thestumbler/serial-squid/docs/squid-pinouts.ods

Sheet: PORTS
SEQ PORT | SEQ PIN | P176x | PORT | BIT | FUNC1 | FUNC2 | FUNC3
1 | 1 | 46 | 0 | 0 | RD1 | TXD3 | SDA1
2 | 2 | 47 | 0 | 1 | TD1 | RXD3 | SCL1
3 | 3 | 98 | 0 | 2 | TXD0 | AD0.7 | N/A
4 | 4 | 99 | 0 | 3 | RXD0 | AD0.6 | N/A
5 | 5 | 81 | 0 | 4 | I2SRX_CLK | RD2 | CAP2.0
6 | 6 | 80 | 0 | 5 | I2SRX_WS | TD2 | CAP2.1
7 | 7 | 79 | 0 | 6 | I2SRX_SDA | SSEL1 | MAT2.0
8 | 8 | 78 | 0 | 7 | I2STX_CLK | SCK1 | MAT2.1
9 | 9 | 77 | 0 | 8 | I2STX_WS | MISO1 | MAT2.2
10 | 10 | 76 | 0 | 9 | I2SRTX_SDA | MOSI1 | MAT2.3
11 | 11 | 48 | 0 | 10 | TXD2 | SDA2 | MAT3.0
12 | 12 | 49 | 0 | 11 | RXD2 | SCL2 | MAT3.1
13 | N/A | N/A | 0 | 12 | N/A | N/A | N/A
14 | N/A | N/A | 0 | 13 | N/A | N/A | N/A
15 | N/A | N/A | 0 | 14 | N/A | N/A | N/A
16 | 13 | 62 | 0 | 15 | TXD1 | SCK0 | SCK
17 | 14 | 63 | 0 | 16 | RXD1 | SSEL0 | SSEL
18 | 15 | 61 | 0 | 17 | CTS1 | MISO0 | MISO
19 | 16 | 60 | 0 | 18 | DCD1 | MOSI0 | MOSI
20 | 17 | 59 | 0 | 19 | DSR1 |  | SDA1
21 | 18 | 58 | 0 | 20 | DTR1 |  | SCL1
22 | 19 | 57 | 0 | 21 | RI1 |  | RD1
23 | 20 | 56 | 0 | 22 | RTS1 |  | TD1
24 | 21 | 9 | 0 | 23 | AD0.0 | I2SRX_CLK | CAP3.0
25 | 22 | 8 | 0 | 24 | AD0.1 | I2SRX_WS | CAP3.1
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
