thestumbler/serial-squid/docs/connector-figure-with-table.odp

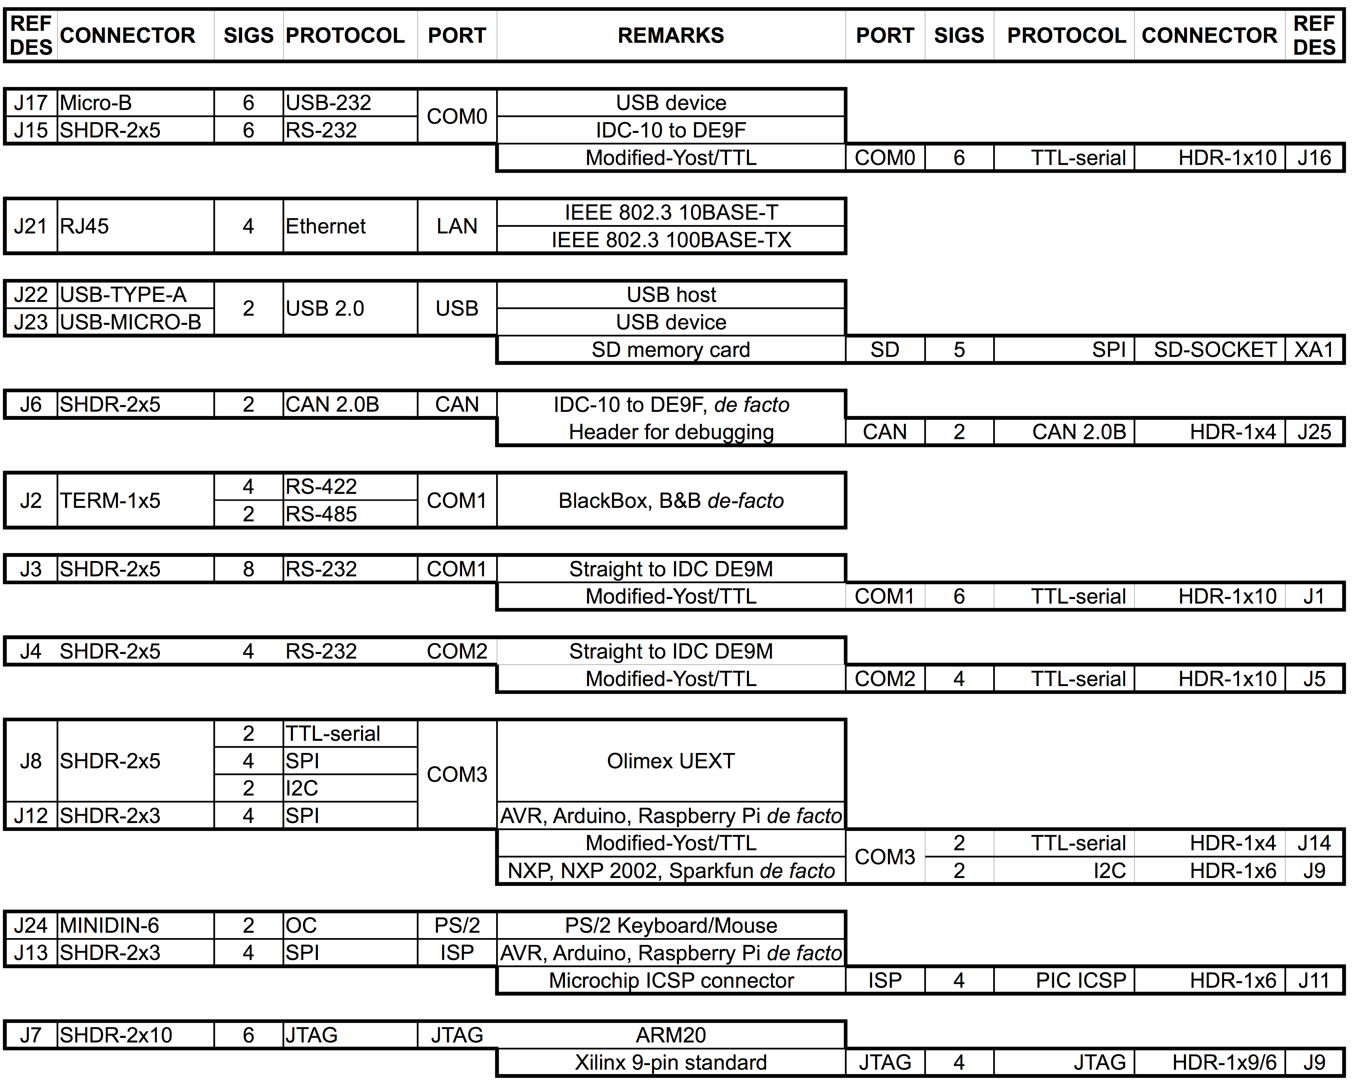
[picture p1: figure]

Serial Squid - Interface Connections

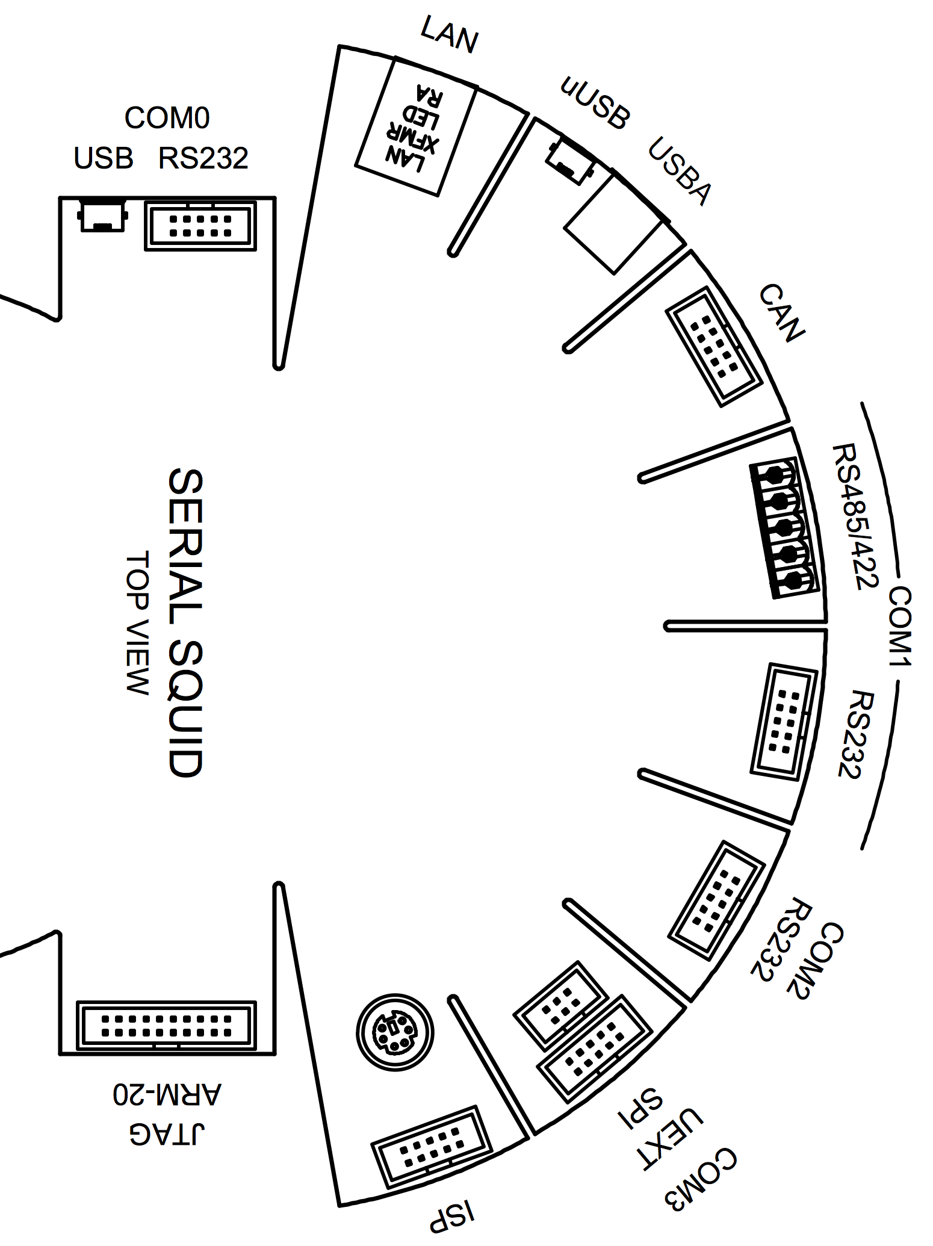
[picture p2: figure]
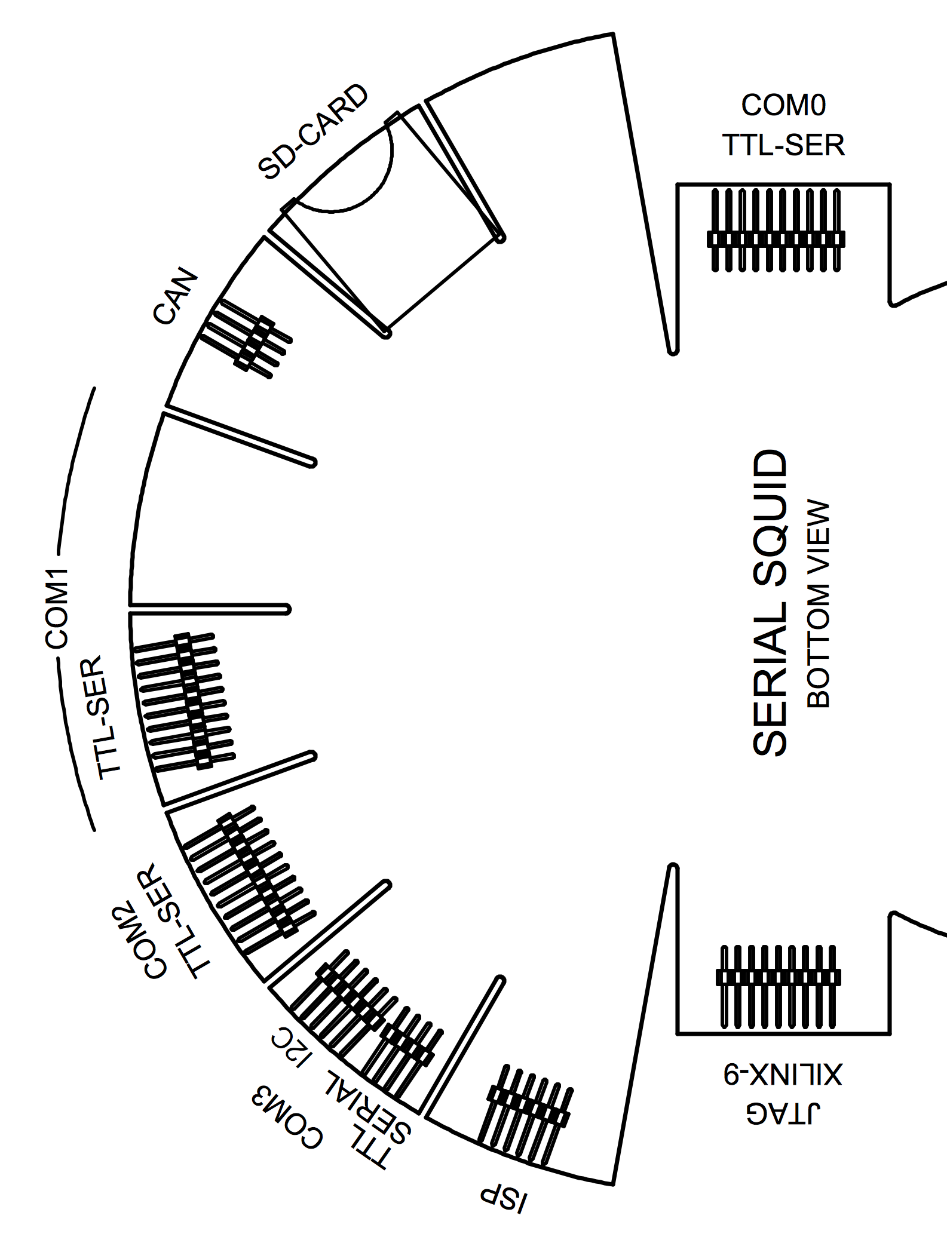
[picture p3: figure]
