thestumbler/serial-squid/parts/con-sd5020-sd-card-socket-smt.pdf

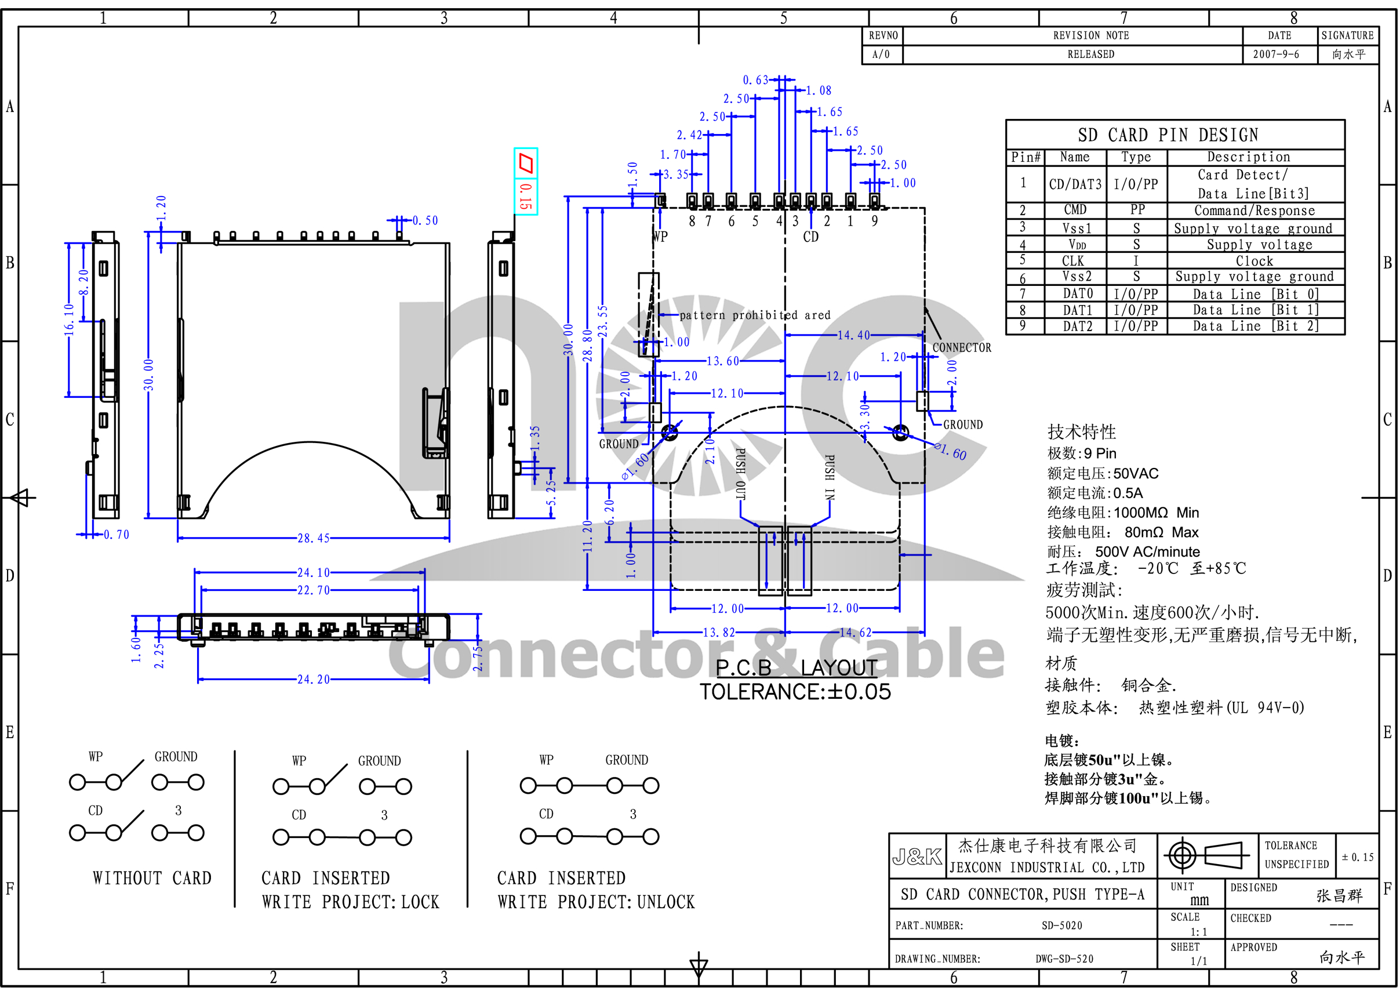
[picture p9: page 1]
