thestumbler/serial-squid/parts/usb-type-a-flat.pdf

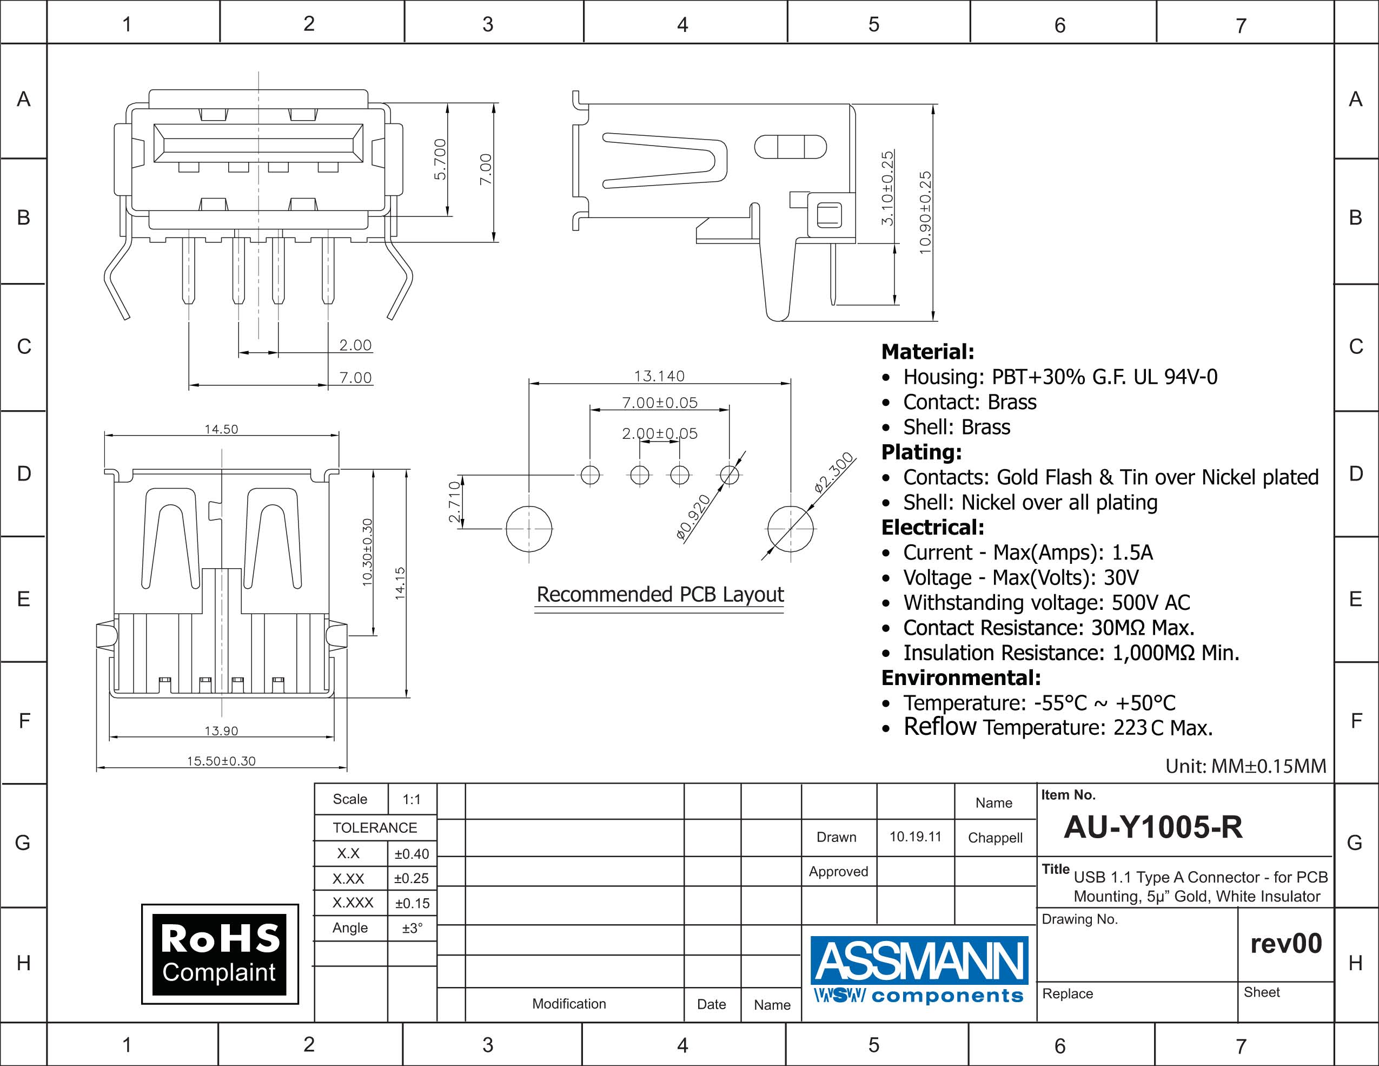
[picture p10: page 1]
