thestumbler/serial-squid/parts/pkg-diodes-inc-SOT23.jpg

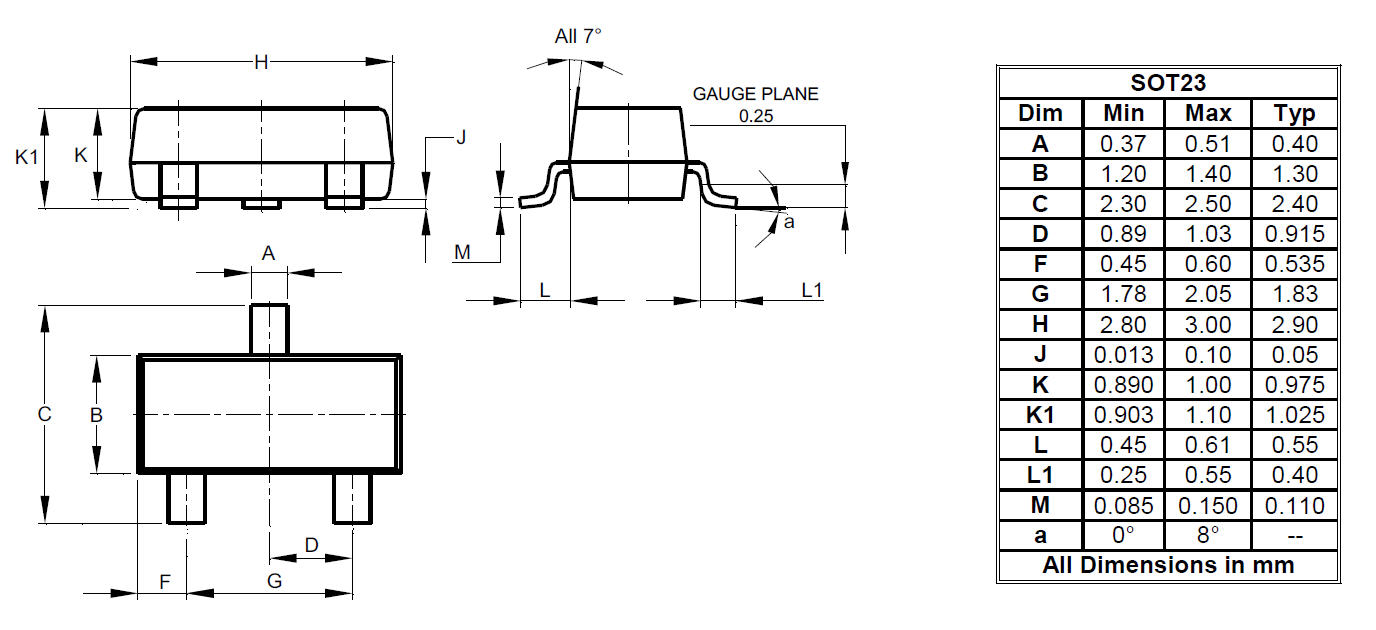
parts/pkg-diodes-inc-SOT23.jpg
