thestumbler/serial-squid/parts/pkg-diodes-inc-SOT323.jpg

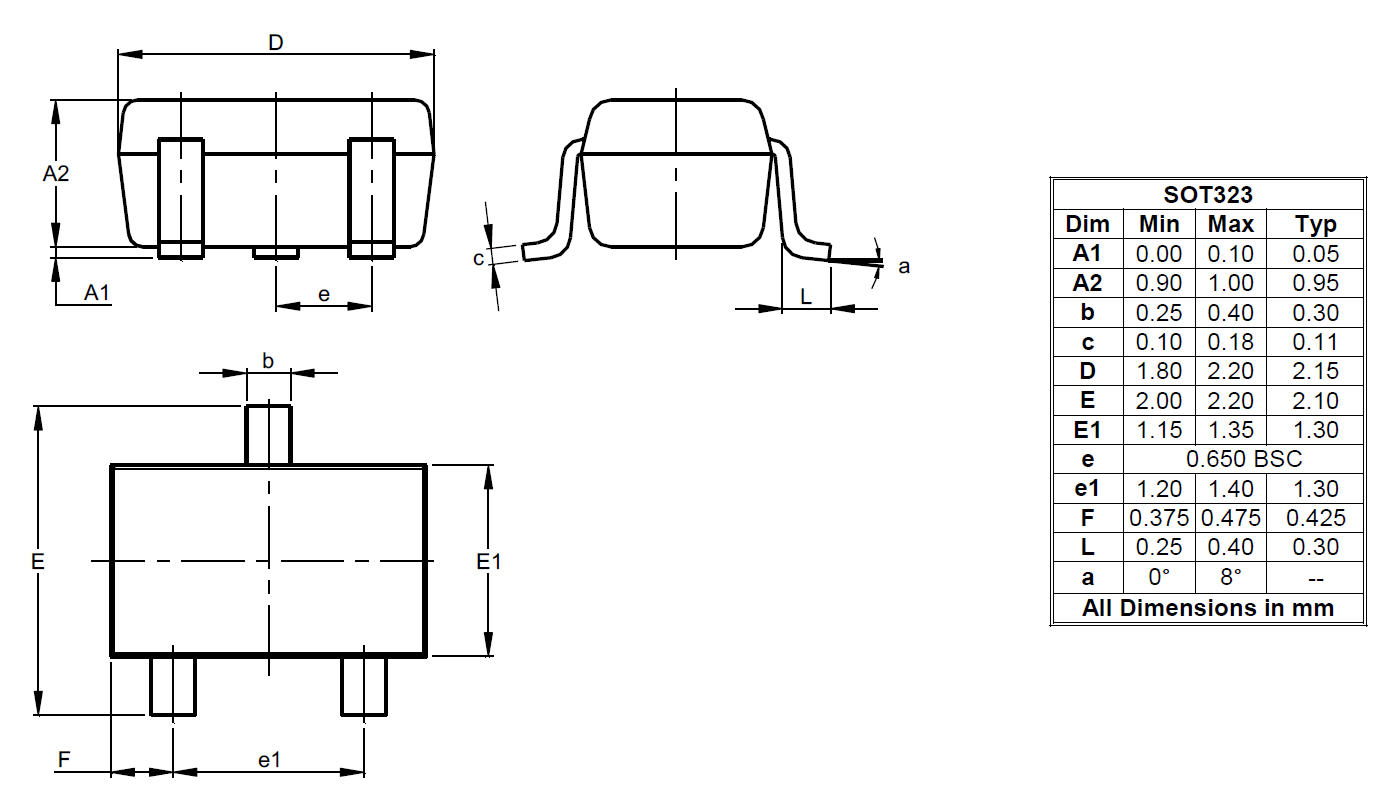
parts/pkg-diodes-inc-SOT323.jpg
