thestumbler/serial-squid/docs/prints/draft2-bot.png

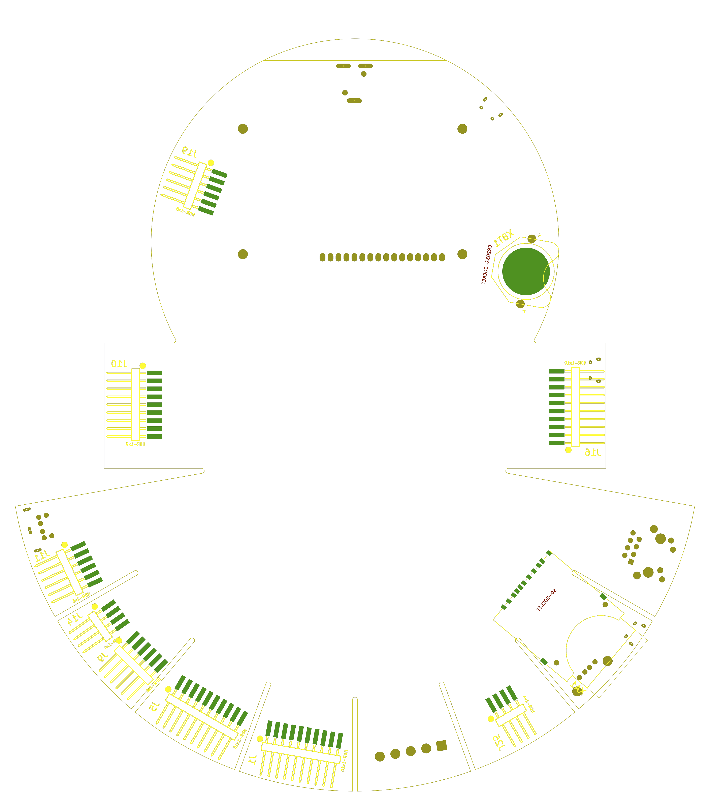
docs/prints/draft2-bot.png
