thestumbler/serial-squid/mech/squid-how-to-draw.png

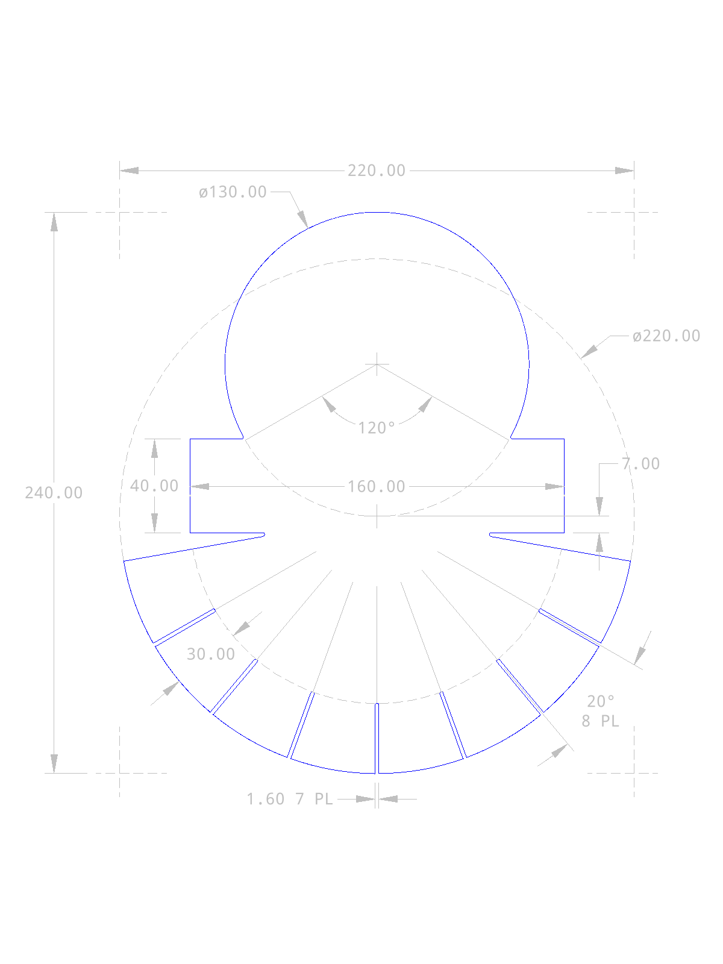
mech/squid-how-to-draw.png
