thestumbler/serial-squid/docs/connector-figure.pdf

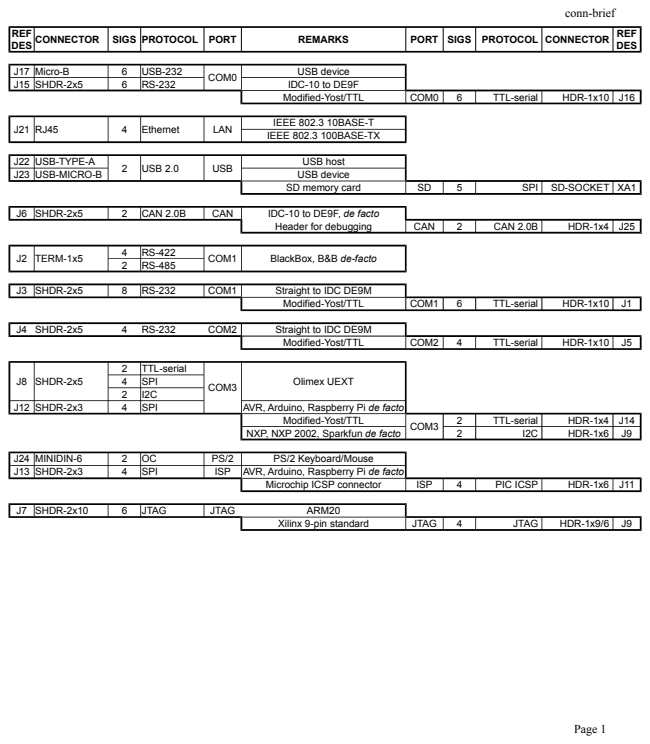
[picture p16: page 1]

IDC-10 to DE9F, de facto

AVR, Arduino, Raspberry Pi de facto

NXP, NXP 2002, Sparkfun de facto
