thestumbler/serial-squid/docs/squid-drawing-bot-view.pdf

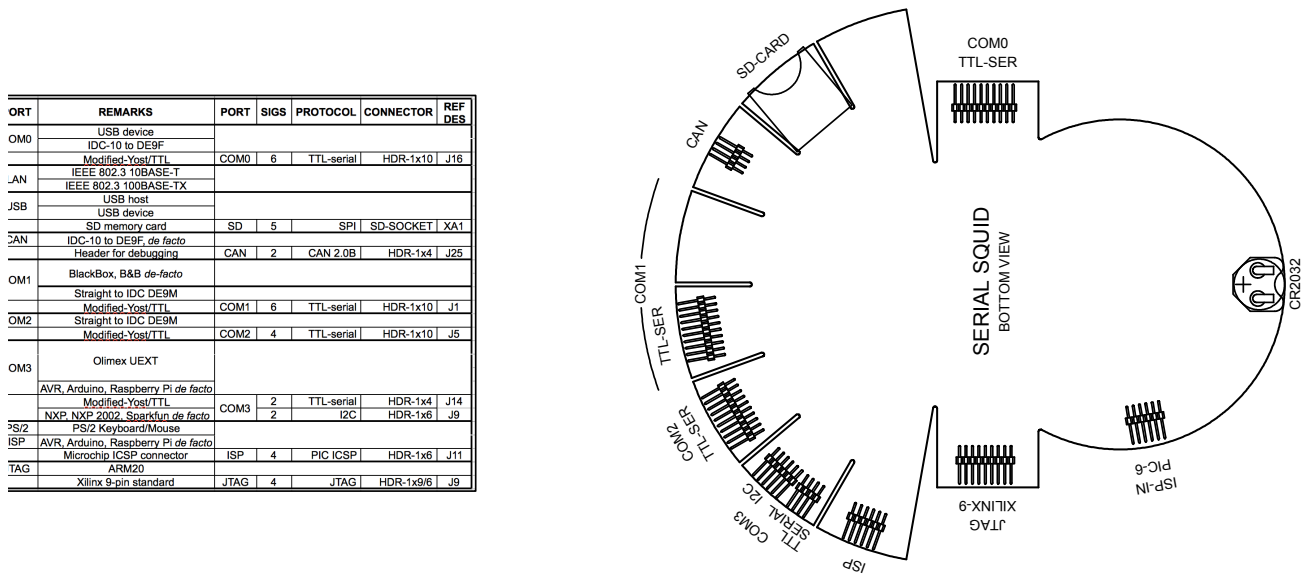
[picture p17: page 1]
I2C COM3; COM0; TTL-SER; SERIAL SQUID; BOTTOM VIEW; COM1; SD-CARD

COM2 TTL-SER TTL-SER CAN
