thestumbler/serial-squid/docs/squid-block-diag.pdf

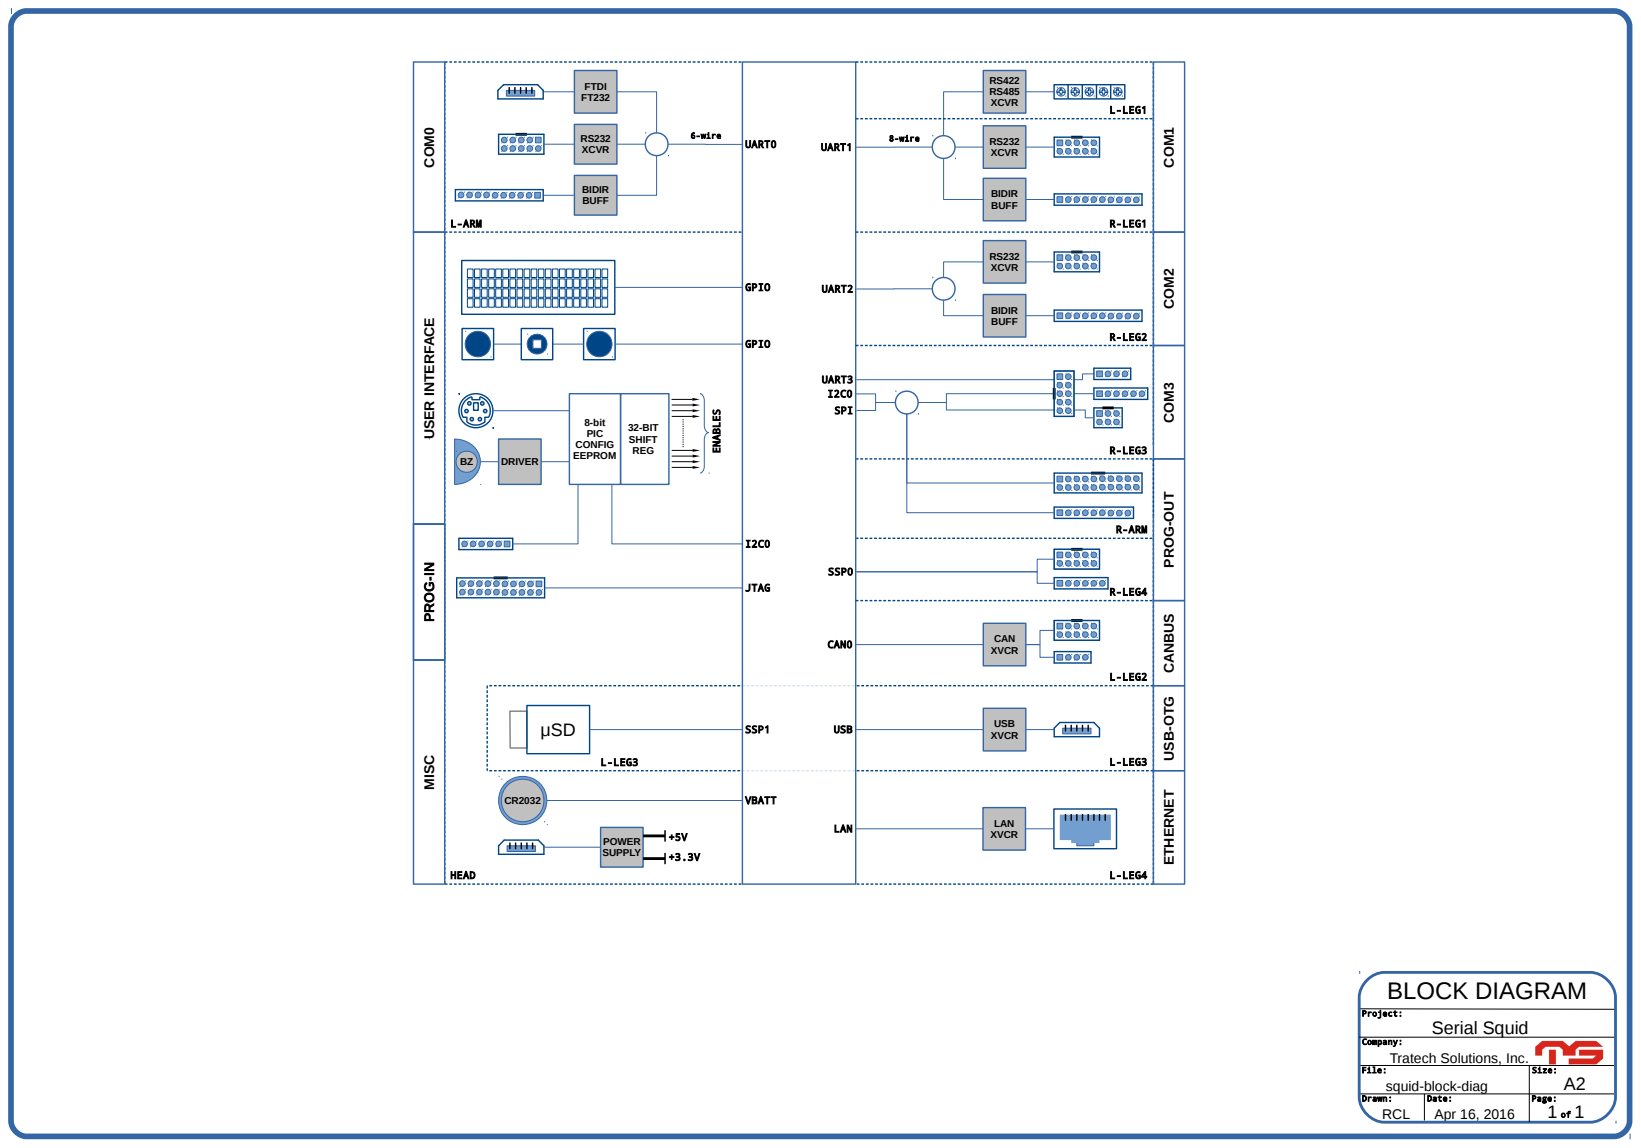
[picture p18: page 1]
RS232 XCVR; BIDIR BUFF; FTDI FT232; UART0; XCVR; RS422 RS485 XCVR; UART1; 8-wire 6-wire; UART2; UART3 I2C0 SPI; SSP0; USB XVCR USB; LAN XVCR LAN; CAN XVCR CAN0; μSD; SSP1; 8-bit PIC CONFIG EEPROM; 32-BIT SHIFT REG; ENABLES; GPIO; JTAG; POWER SUPPLY; VBATT; L-ARM; HEAD; L-LEG4; L-LEG3; L-LEG2; R-ARM; R-LEG4; R-LEG3; R-LEG2; R-LEG1; L-LEG1; DRIVER; Drawn:; Date:; Project:; Apr 16, 2016; Serial Squid; Page:; BLOCK DIAGRAM; Size:

COM0 USER INTERFACE PROG-IN MISC PROG-IN

COM1 COM2 COM3 PROG-OUT CANBUS ETHERNET USB-OTG

Company:
Tratech Solutions, Inc.
File:
squid-block-diag
RCL
