thestumbler/serial-squid/parts/con-rect-1x4-molex.pdf

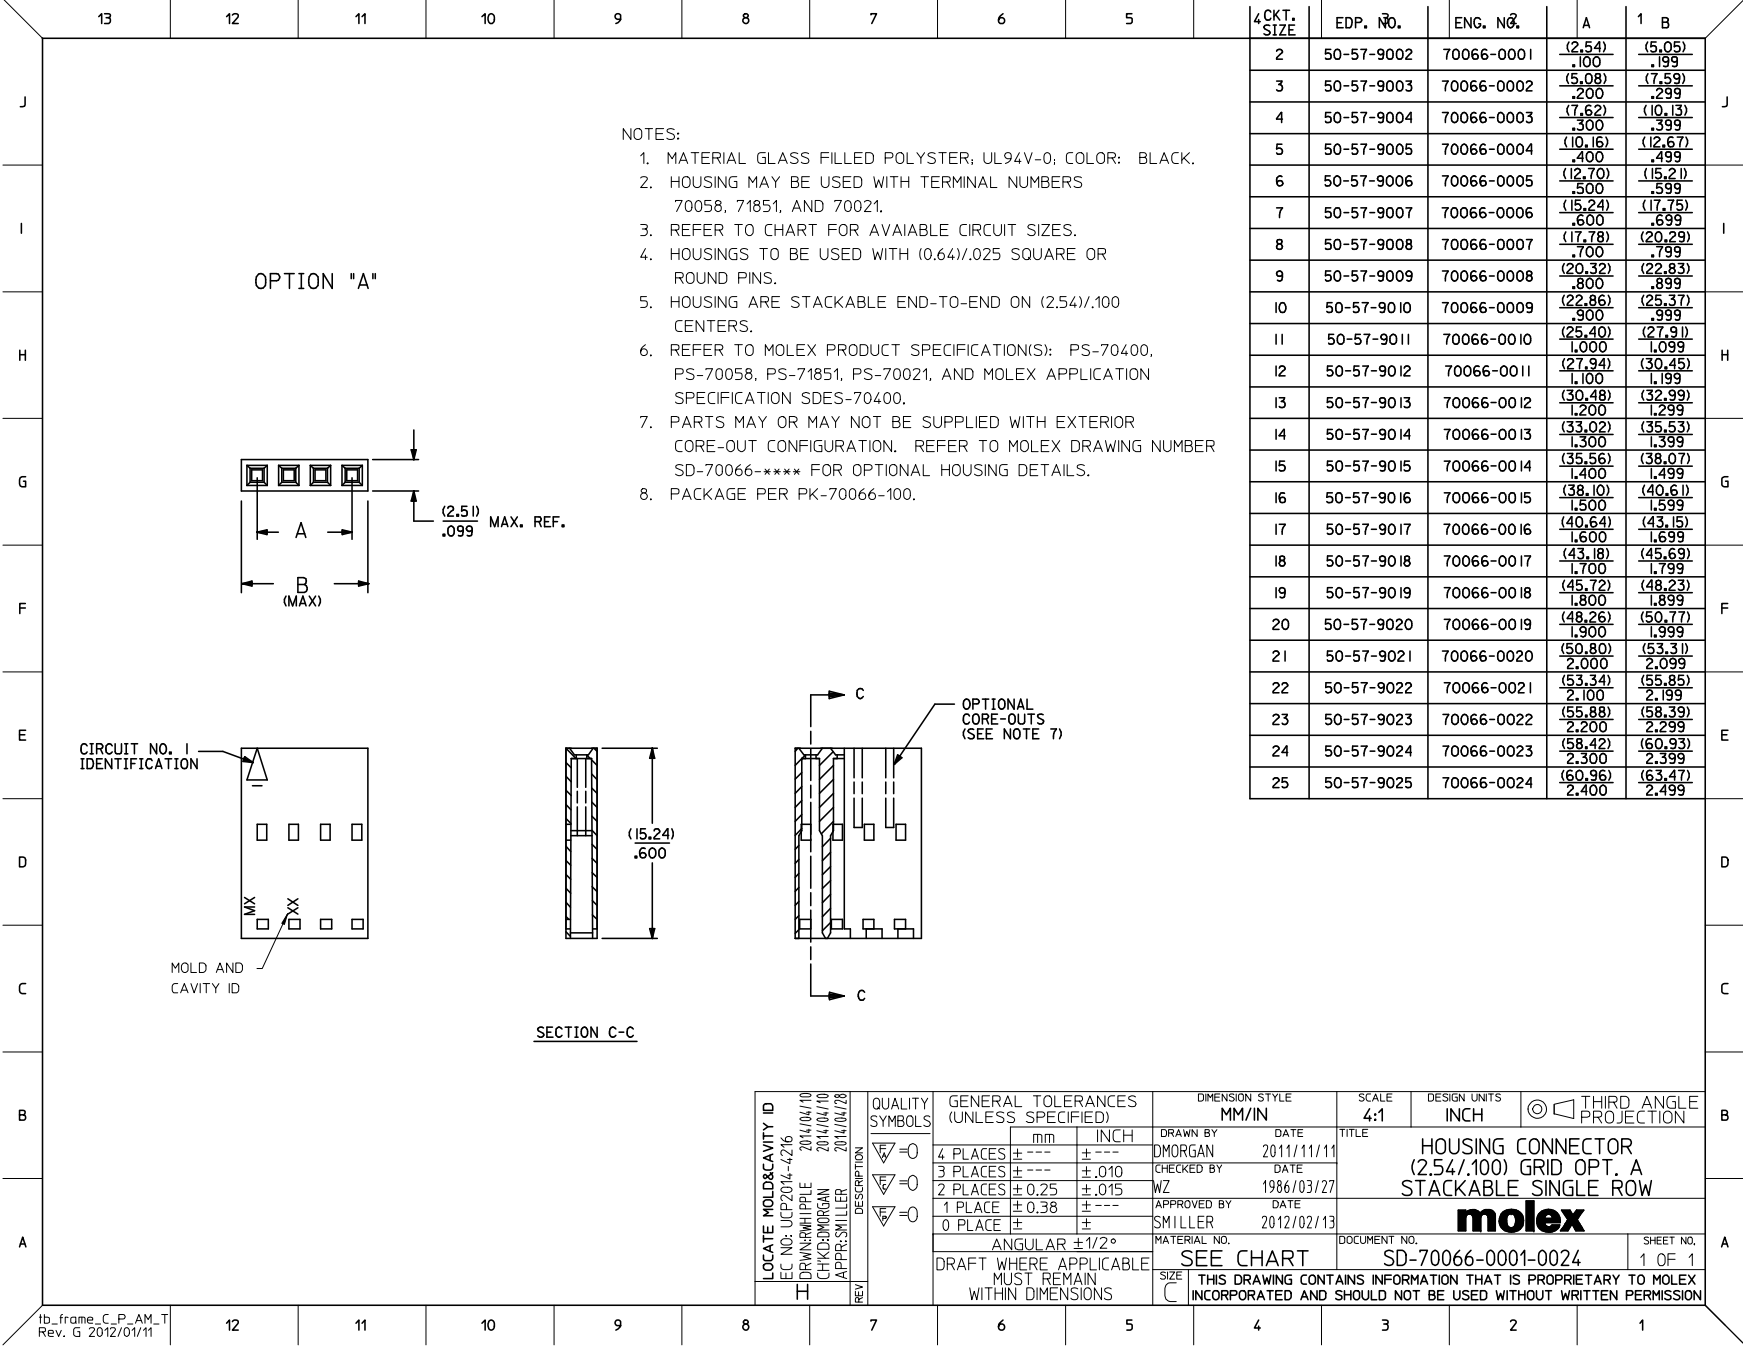
[picture p21: page 1]
