thestumbler/serial-squid/parts/con-usb-typea-smt-cnctech-1003-002-01100.pdf

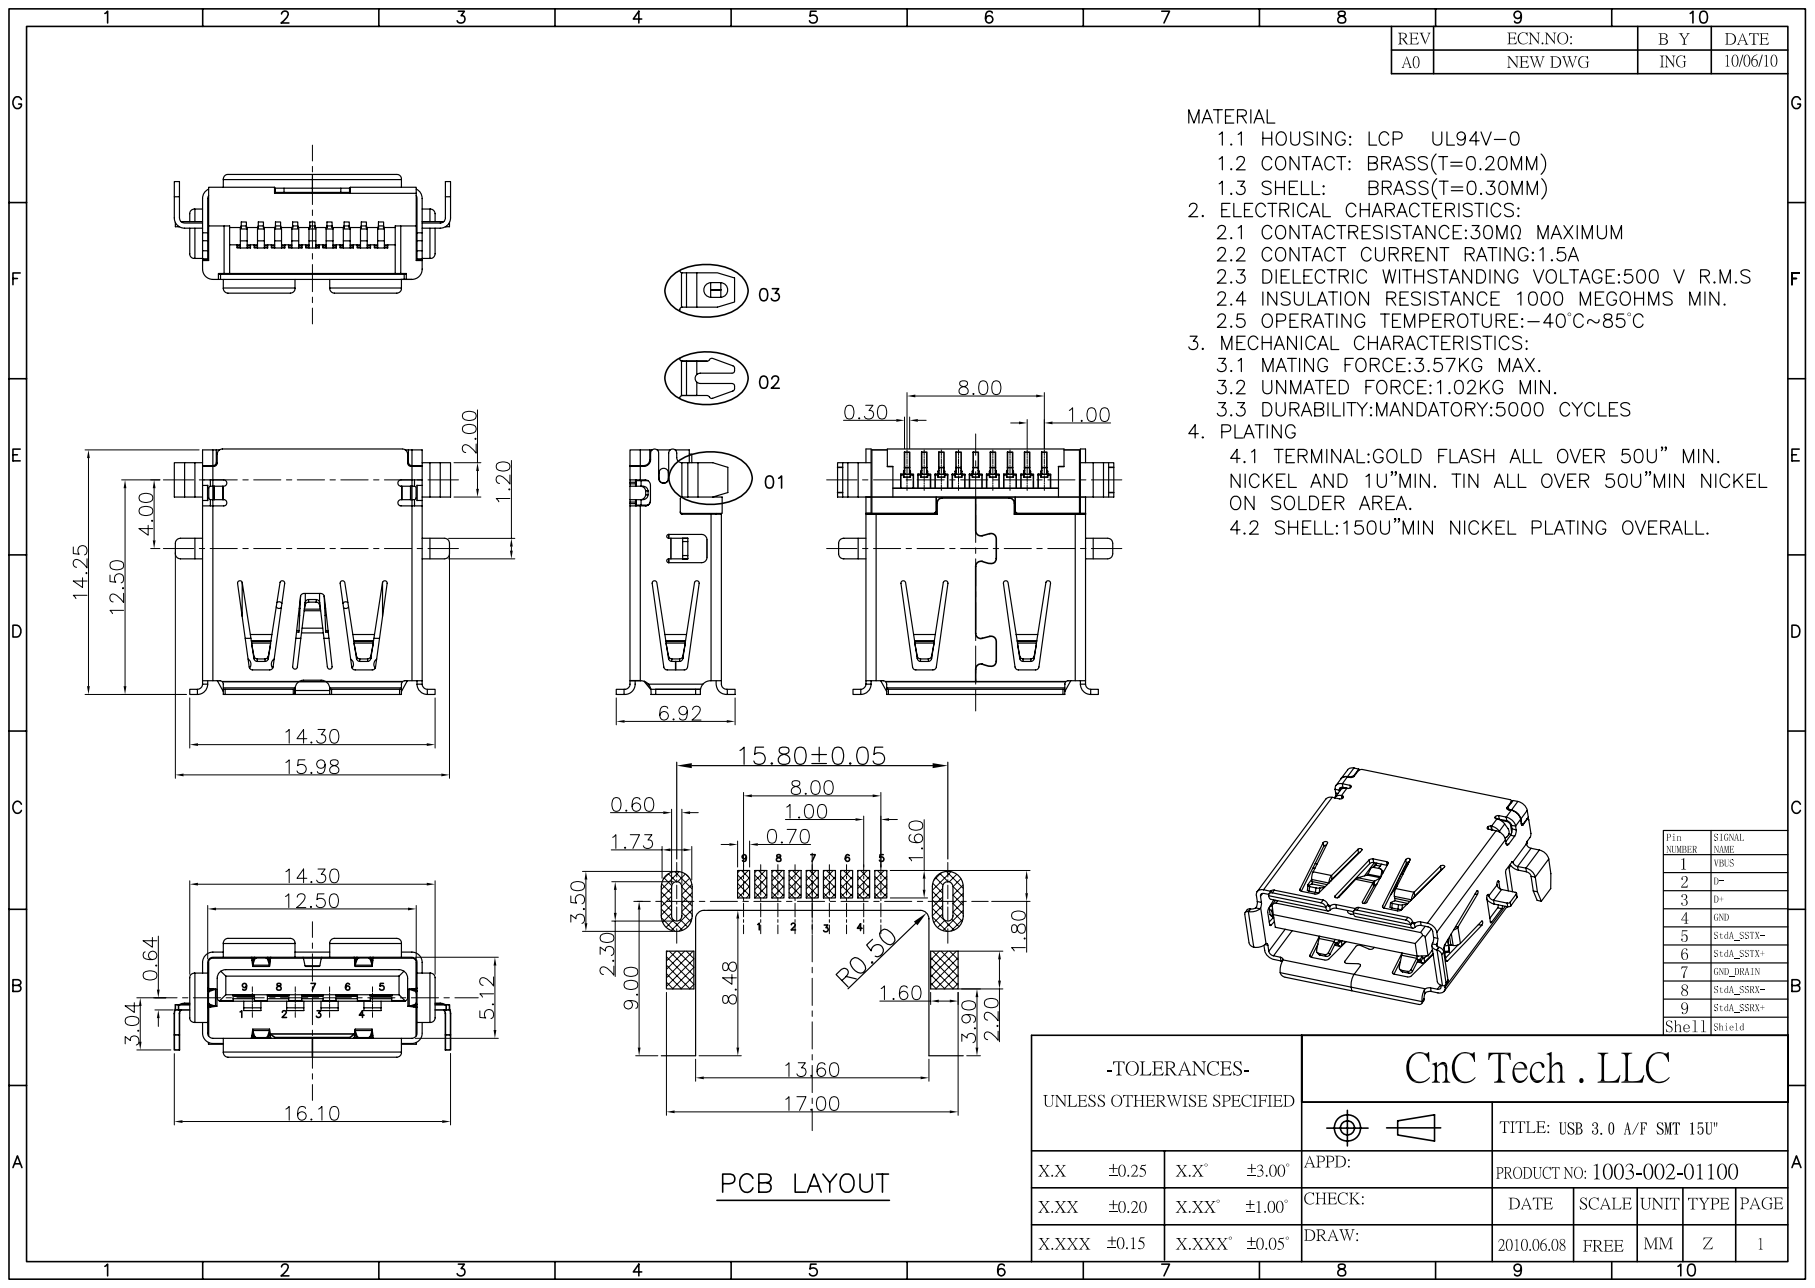
[picture p22: page 1]
