thestumbler/serial-squid/parts/pkg-fairchild-sot23-3l.pdf

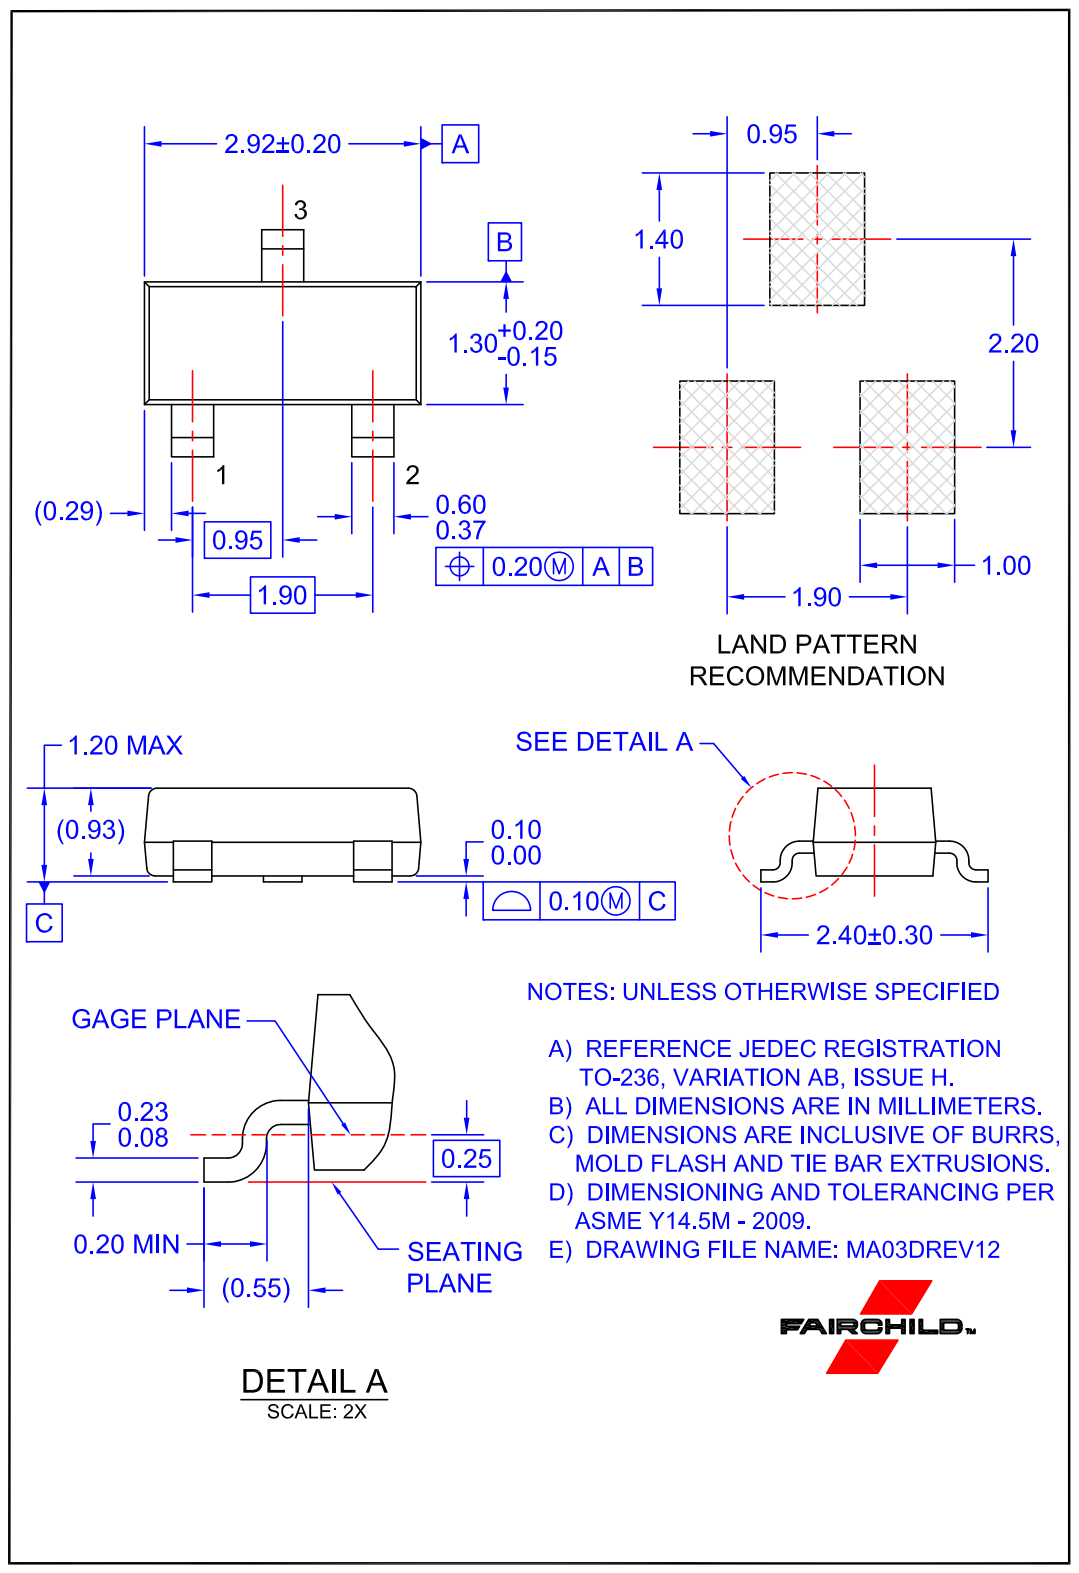
[picture p23: page 1]
