thestumbler/serial-squid/parts/pkg-maxim-a28p1-ssop28-layout.pdf

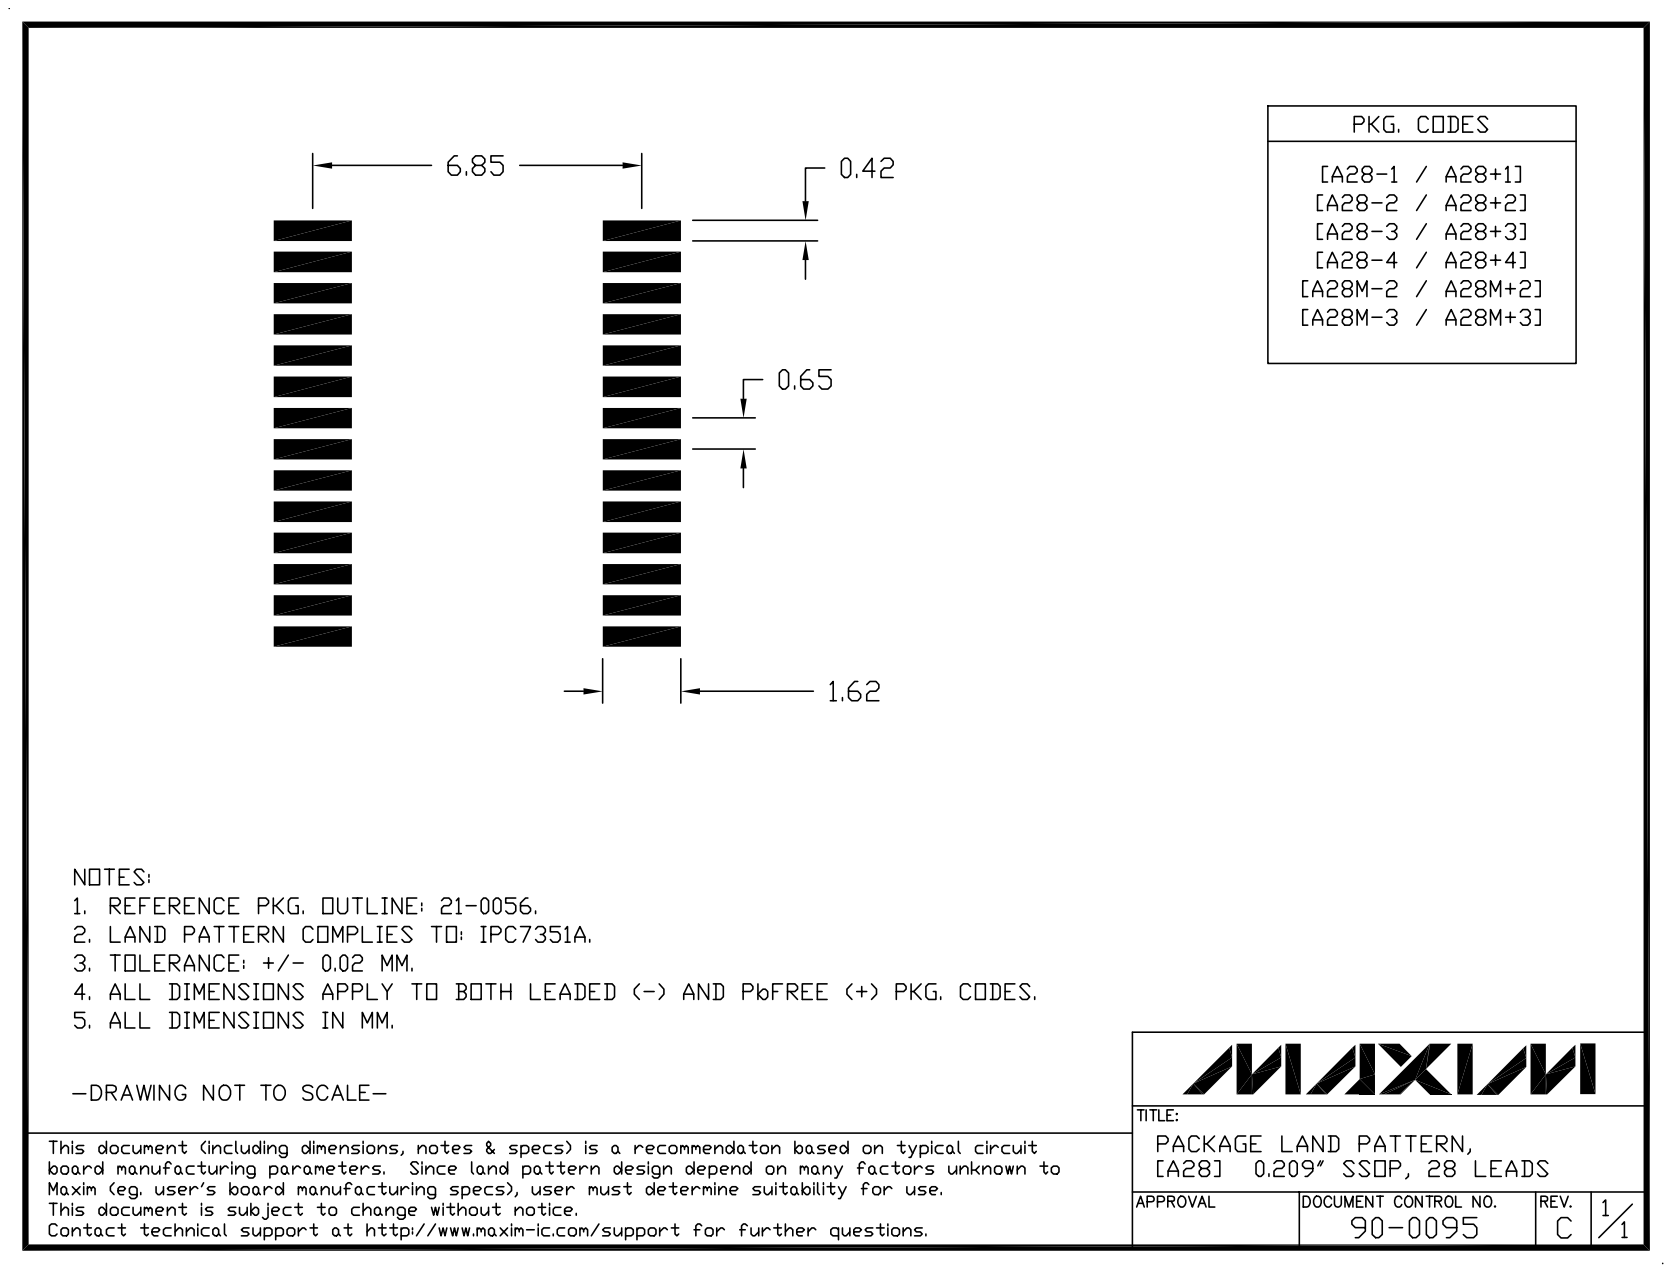
[picture p24: page 1]
