thestumbler/serial-squid/parts/pkg-maxim-a28p1-ssop28.pdf

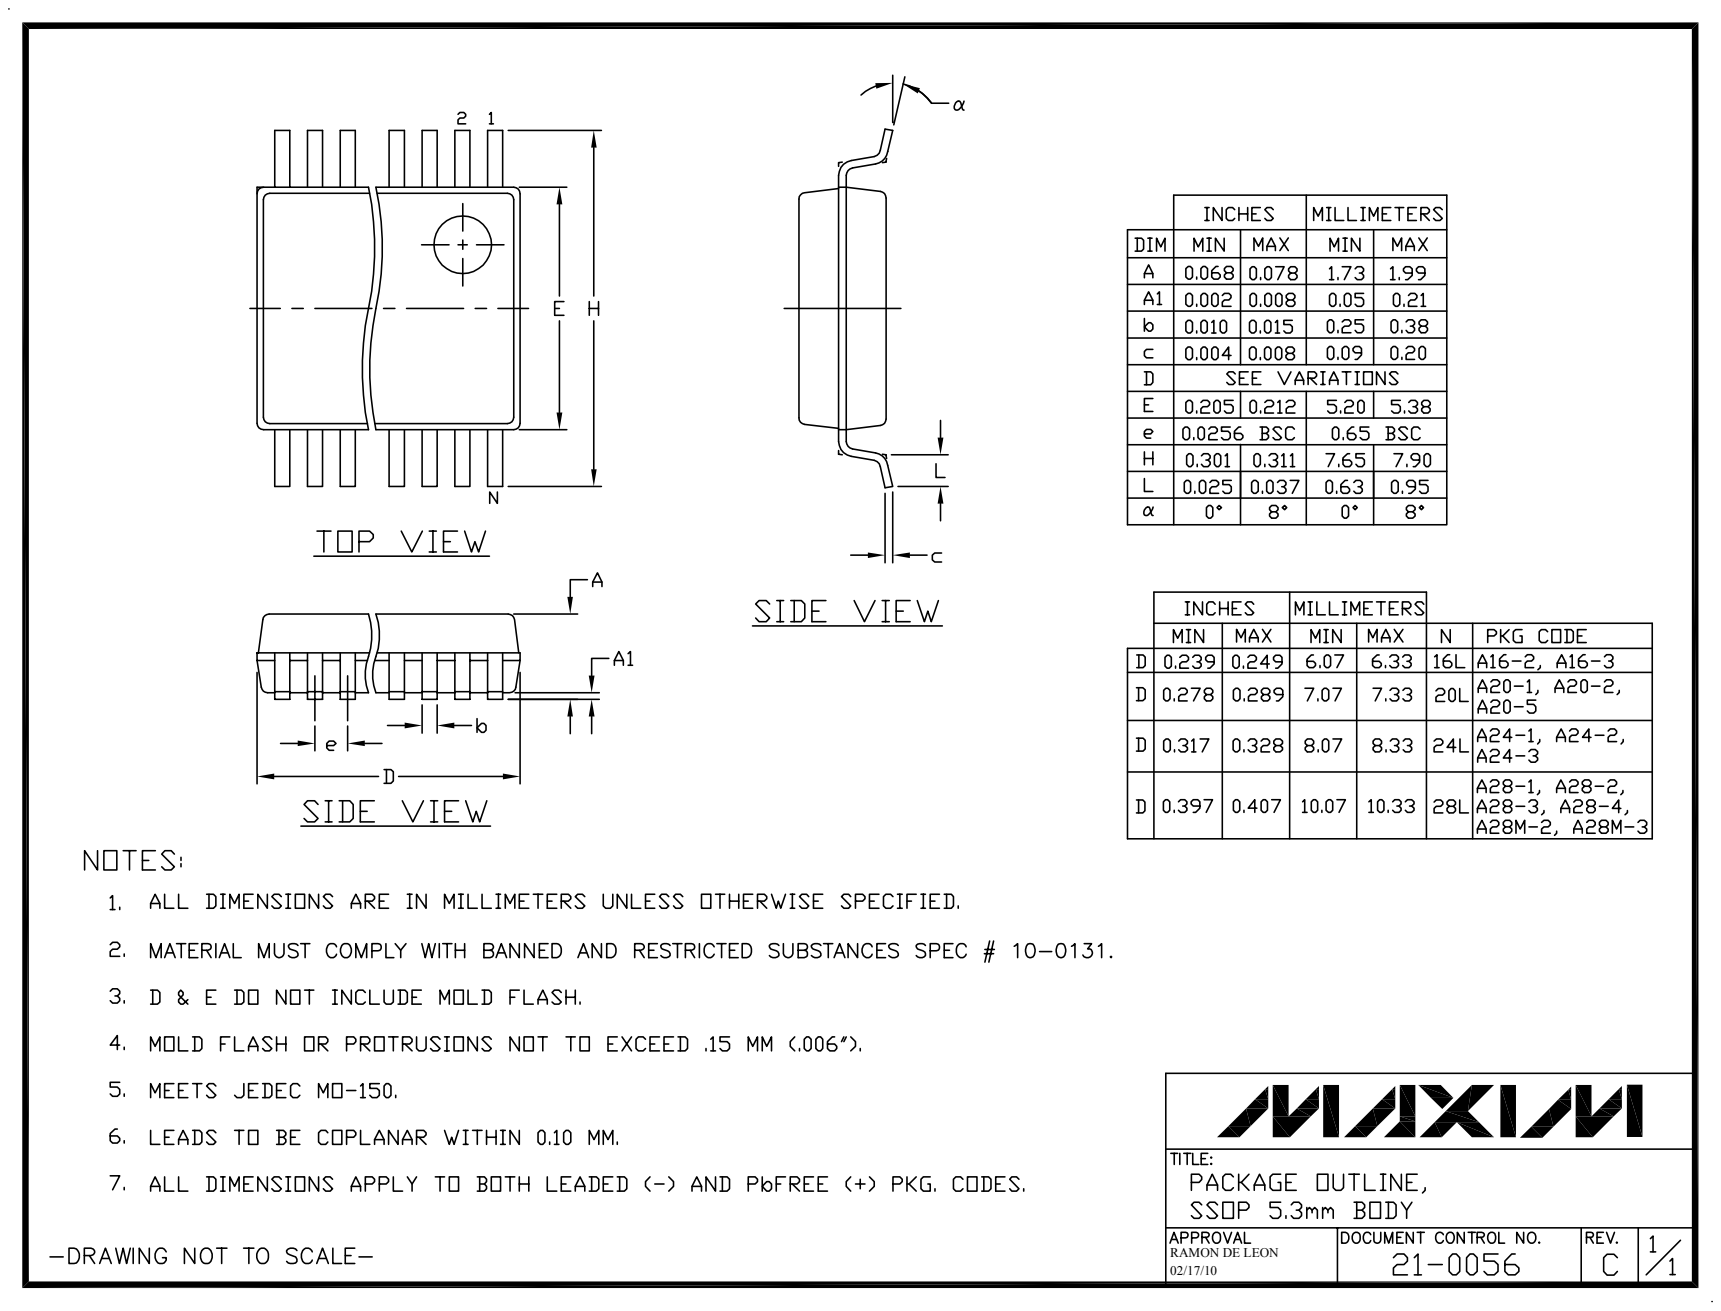
[picture p25: page 1]
