thestumbler/serial-squid/parts/pkg-microchip-sot223-5.pdf

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

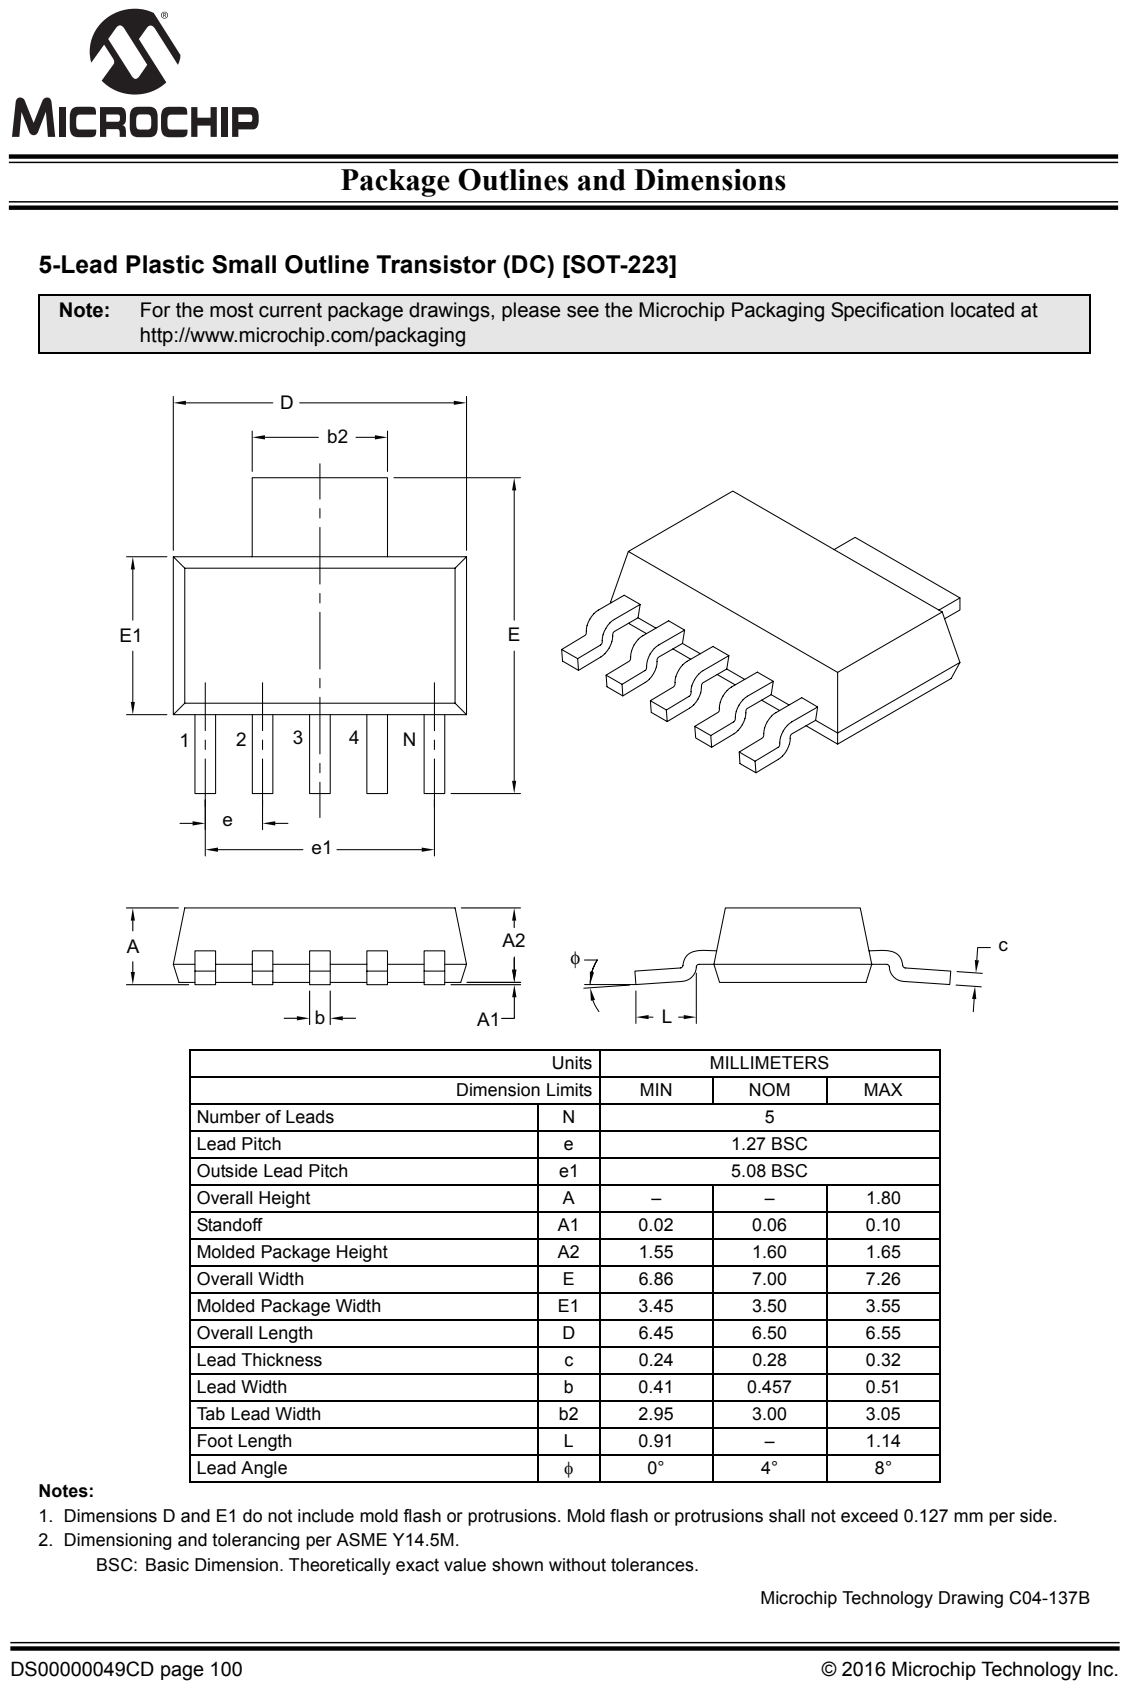
[picture p26: page 1]

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

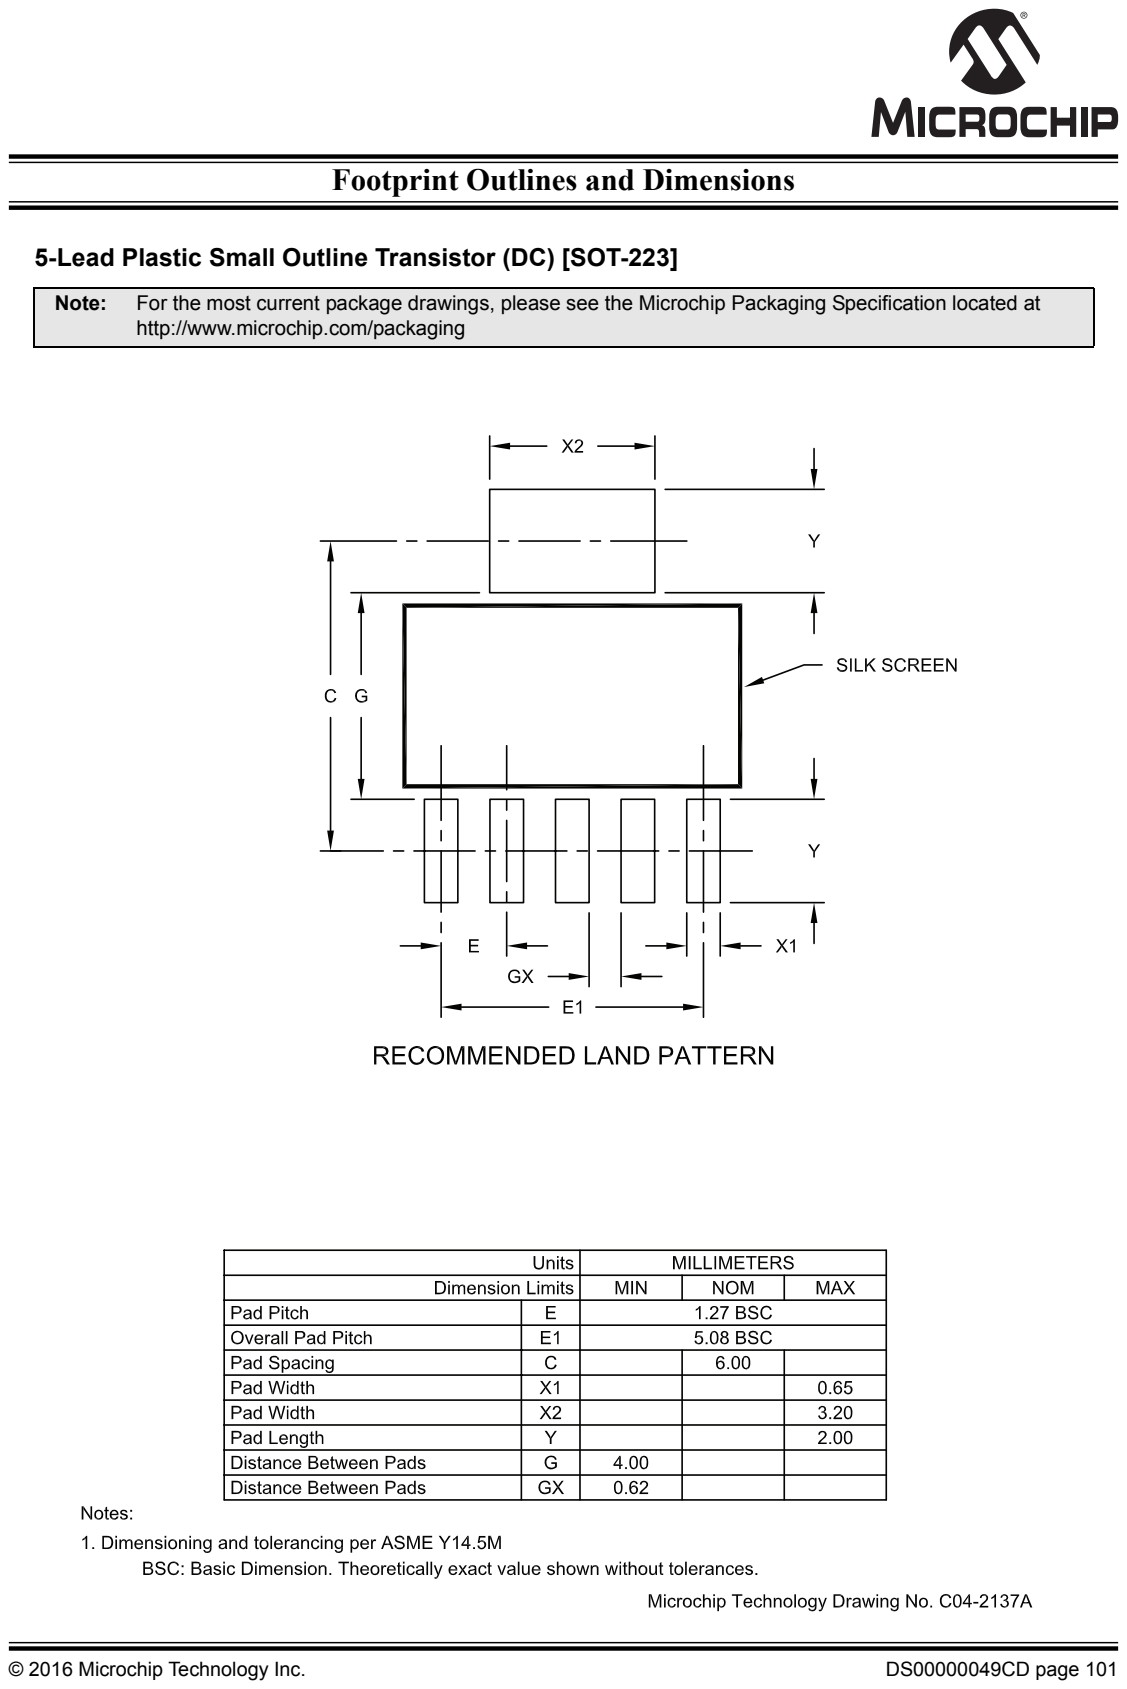
[picture p27: page 2]
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
