thestumbler/serial-squid/parts/pkg-microchip-sot223.pdf

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

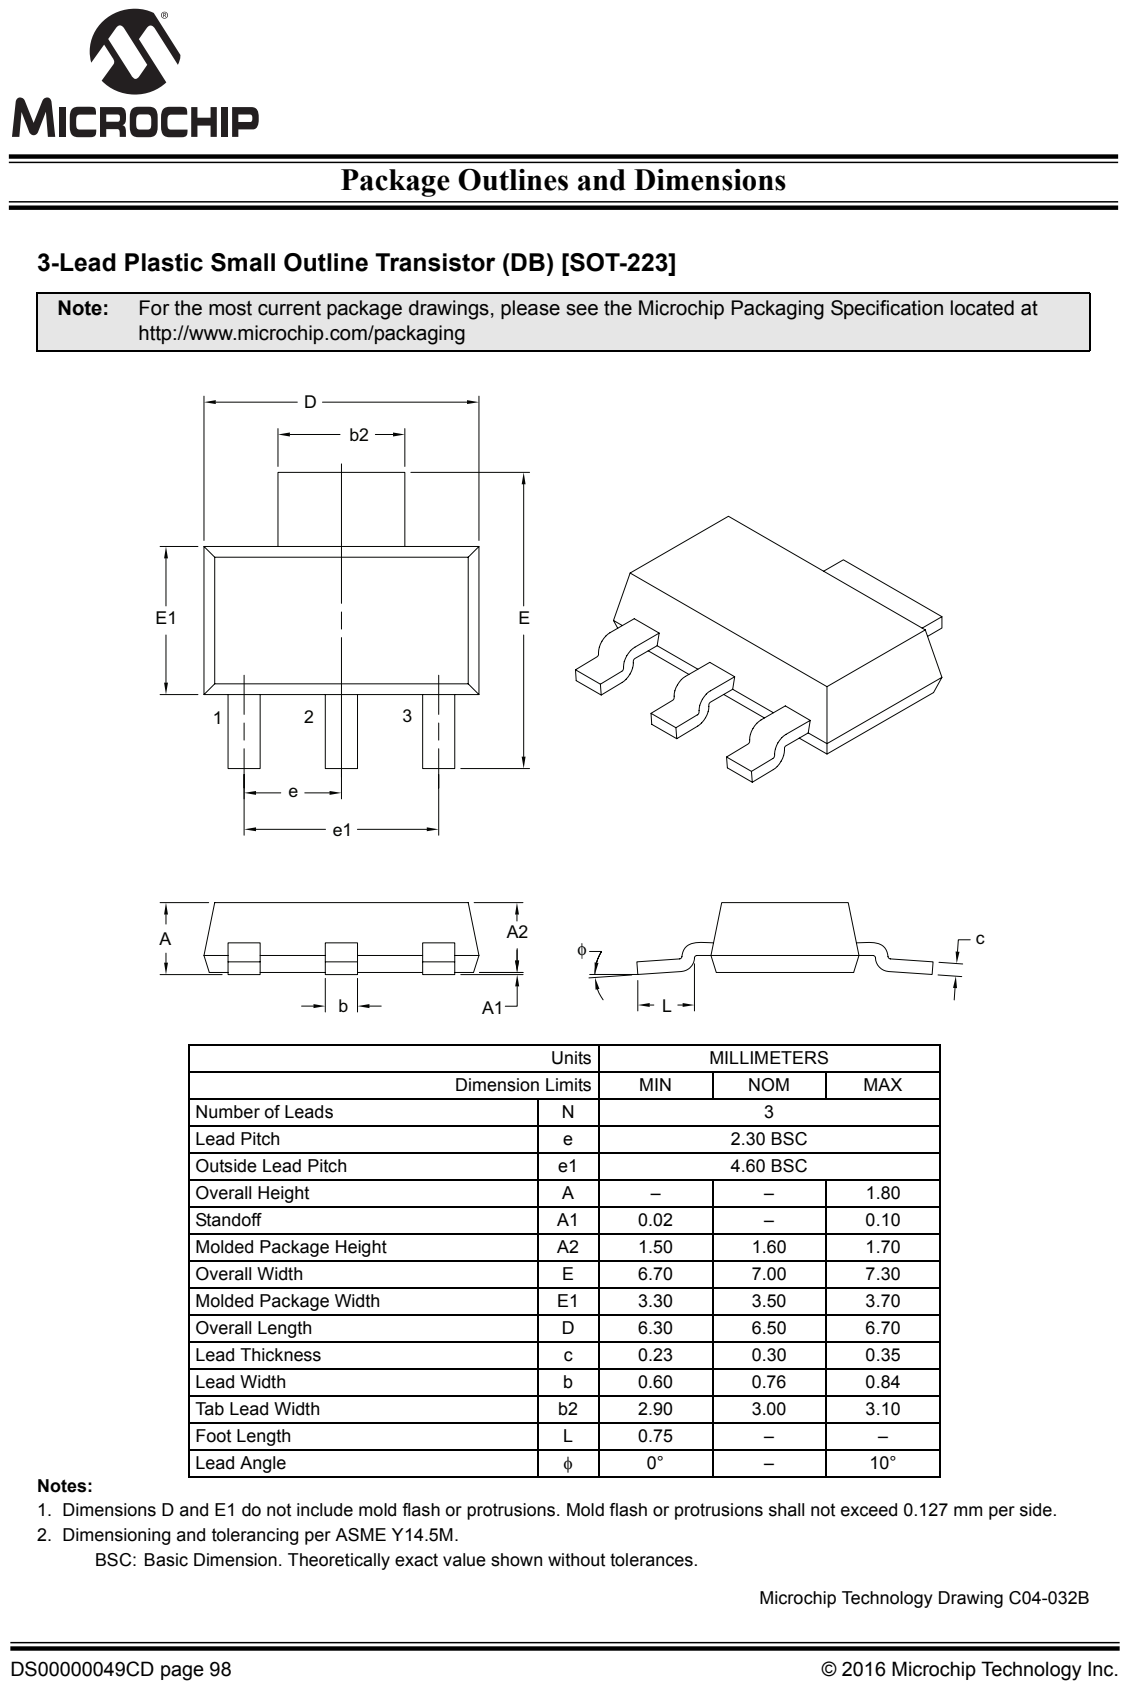
[picture p28: page 1]

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

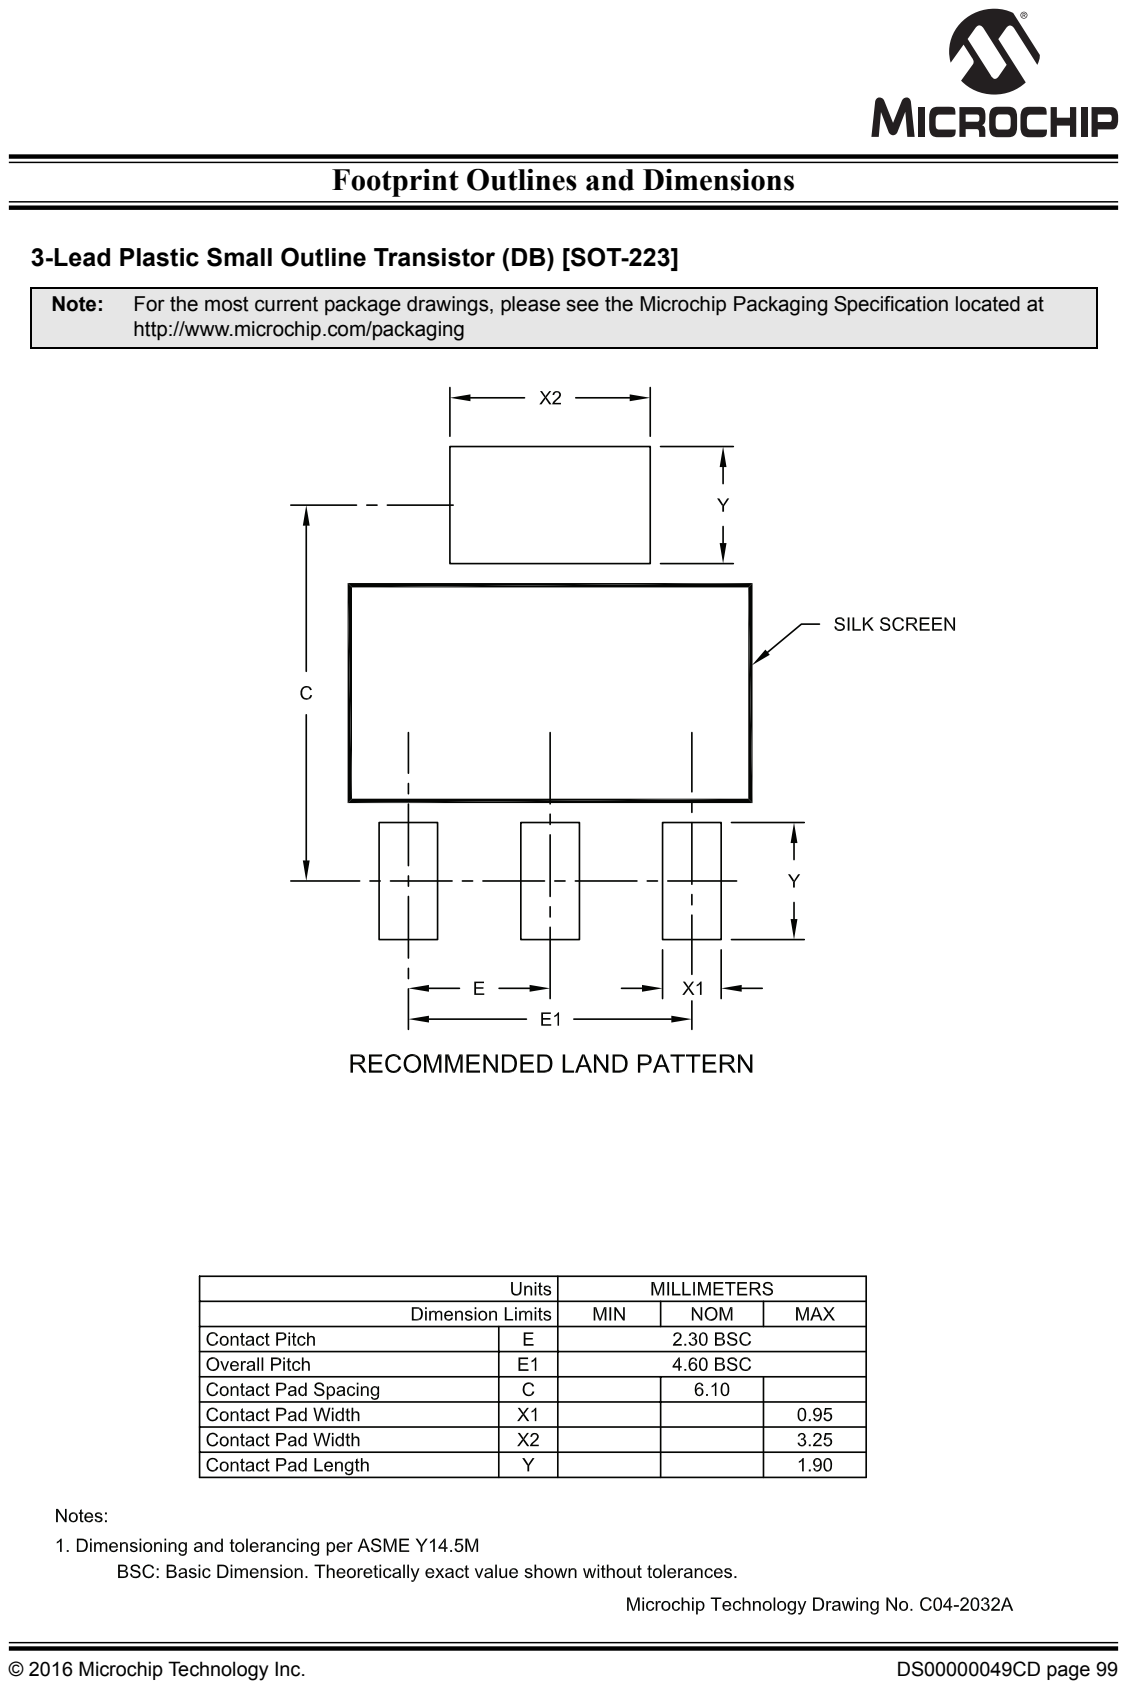
[picture p29: page 2]
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
