thestumbler/serial-squid/parts/usb-micro-flat.pdf

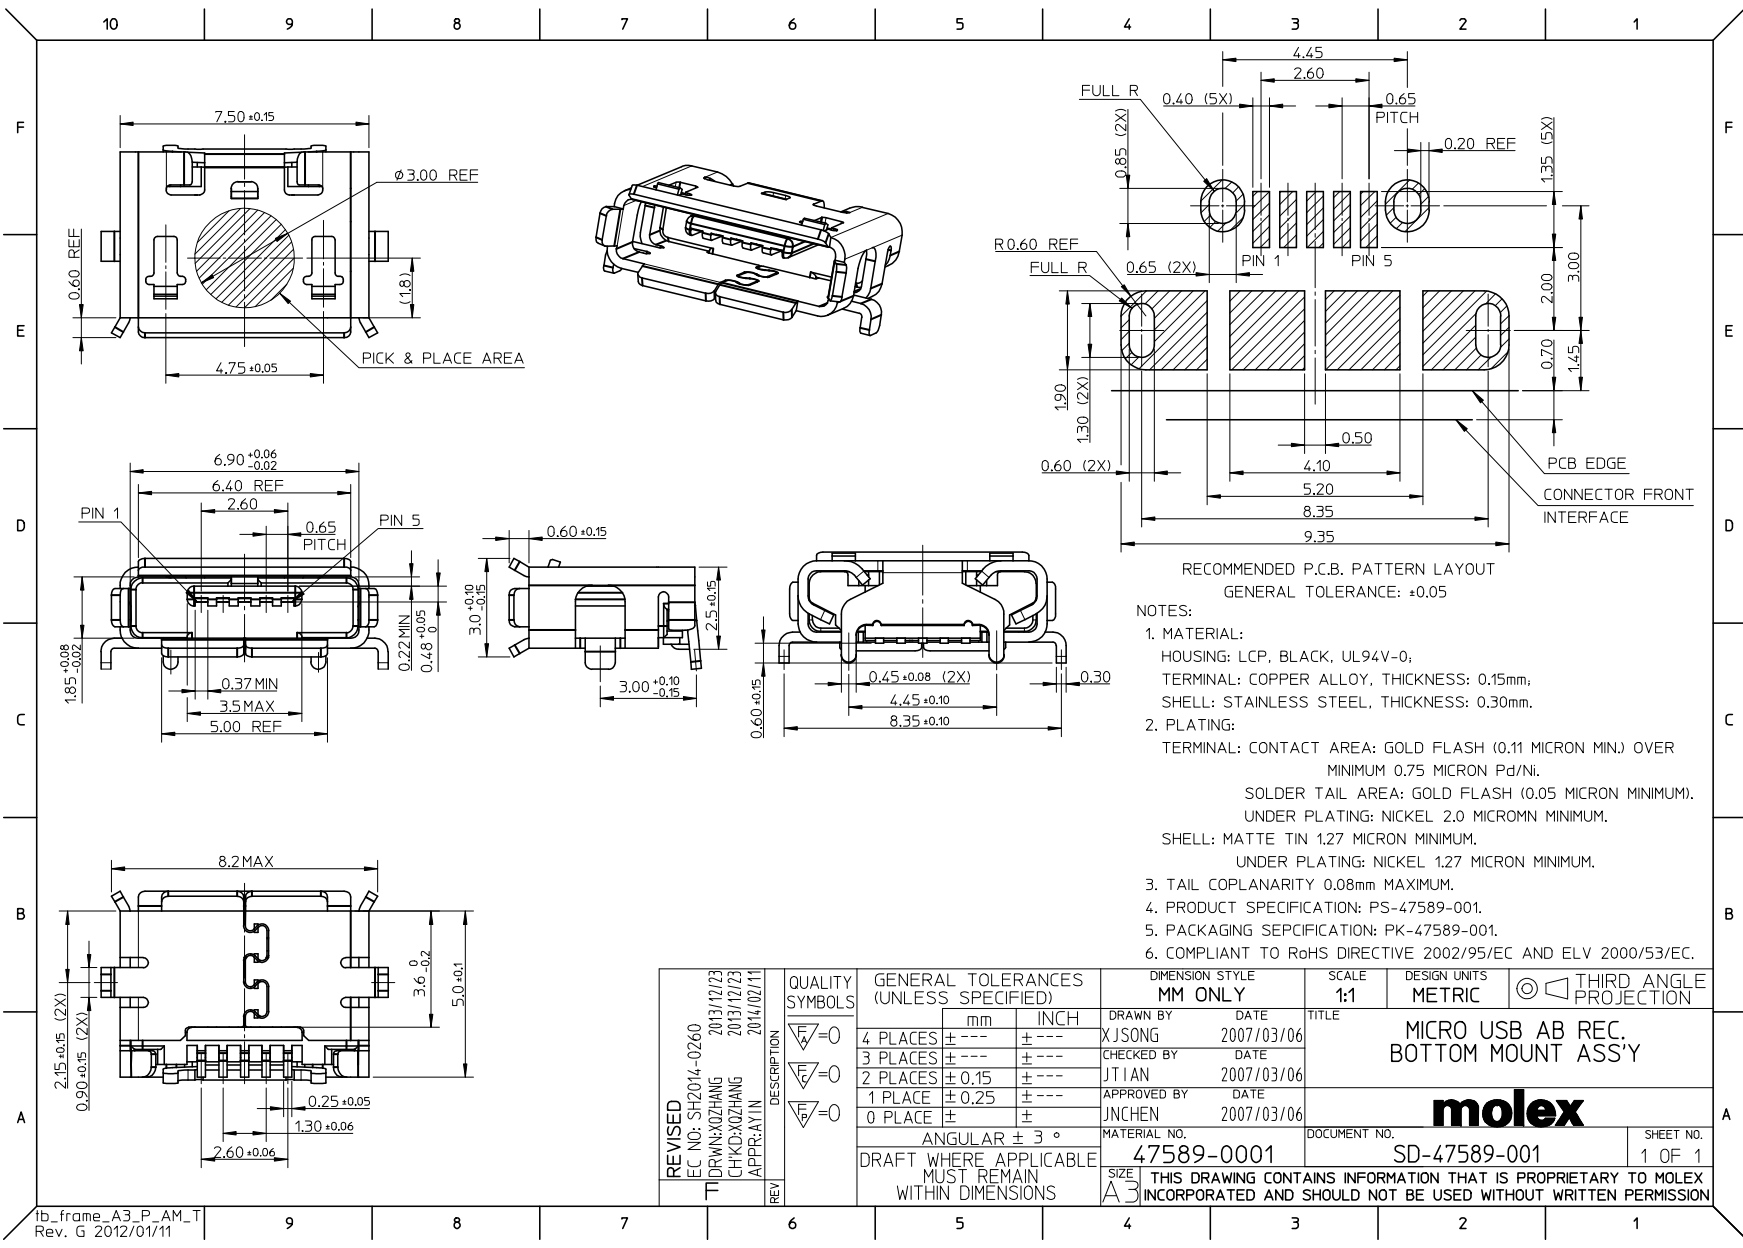
[picture p30: page 1]
