thestumbler/serial-squid/docs/prints/draft2-bot.pdf

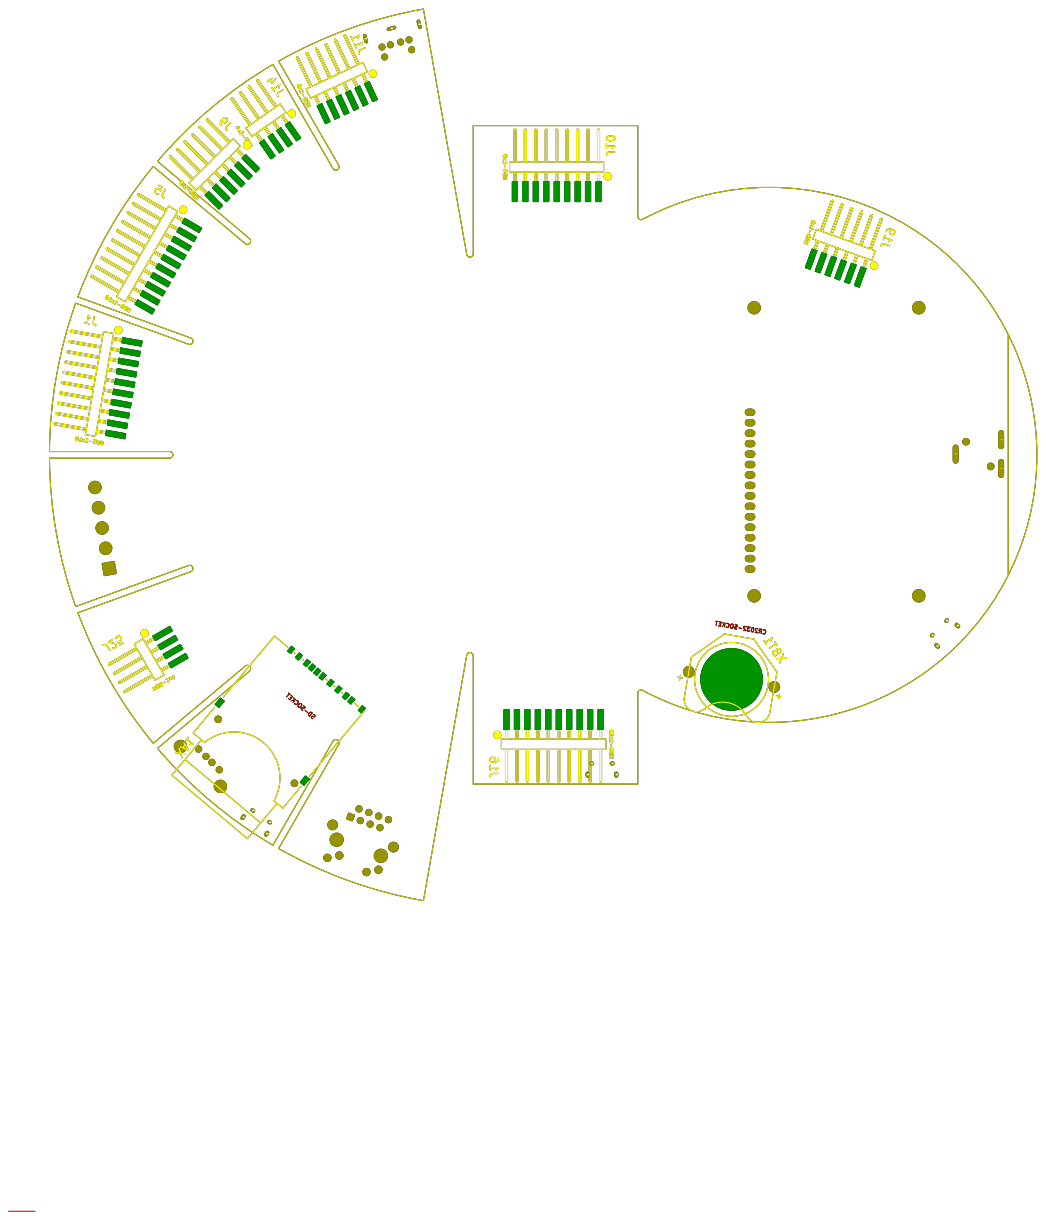
[picture p31: page 1]
