thestumbler/serial-squid/docs/prints/draft2-top.pdf

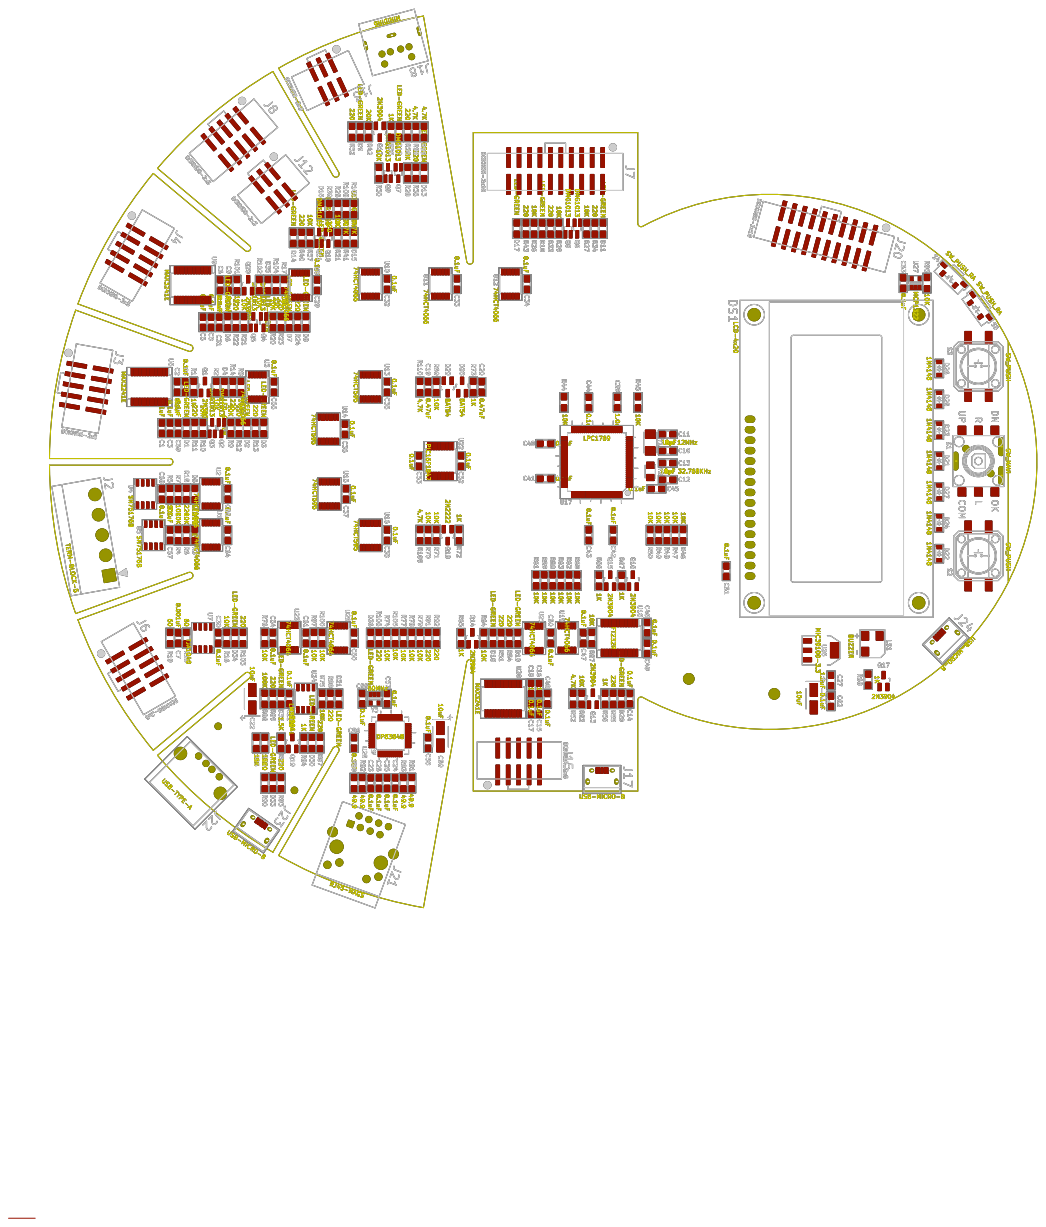
[picture p32: page 1]
