thestumbler/serial-squid/docs/serial-squid-placement-top-draft2.pdf

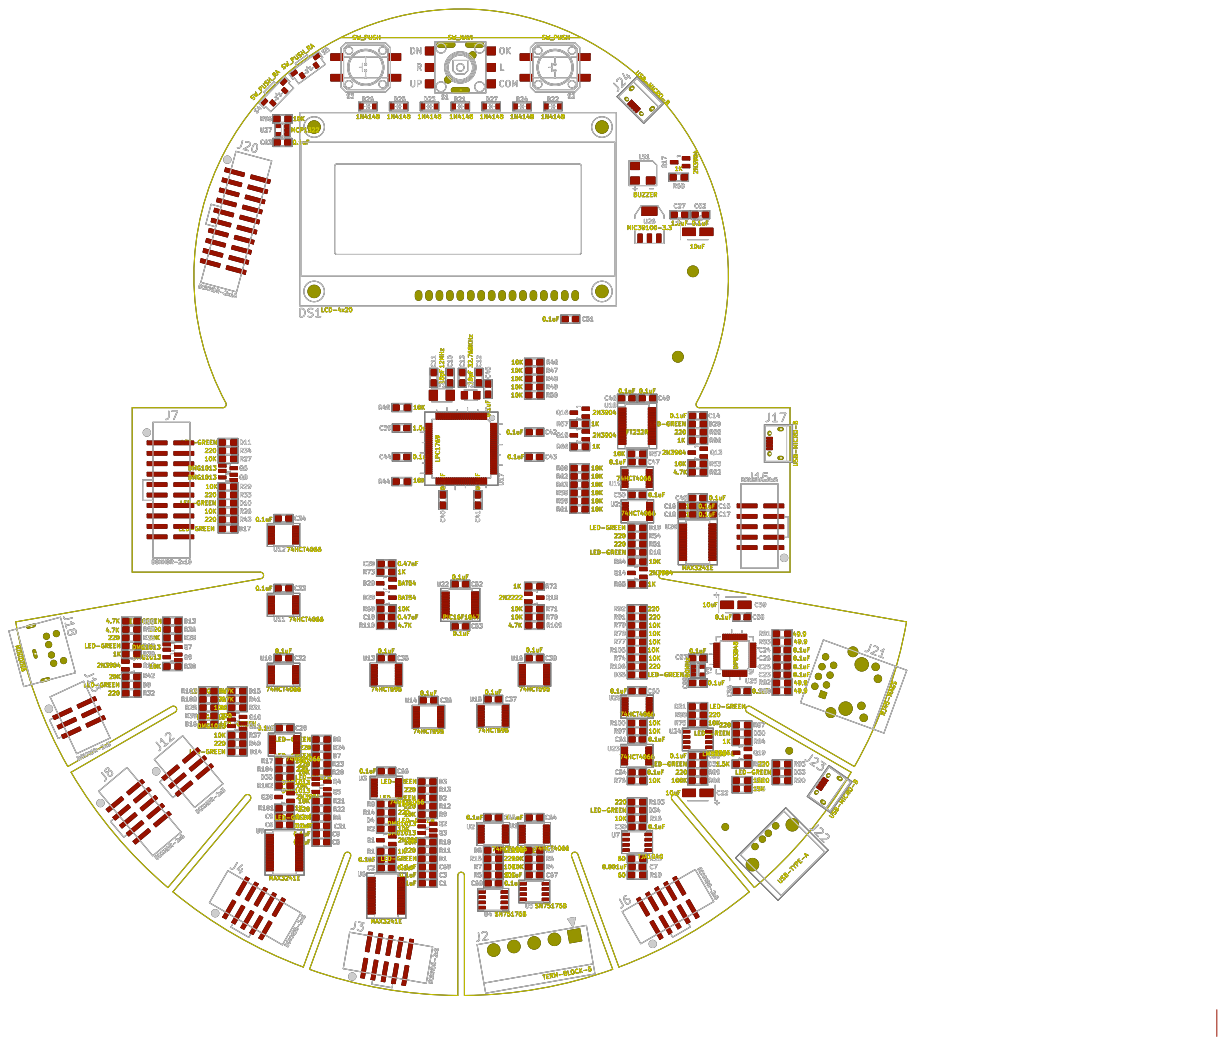
[picture p33: page 1]
