thestumbler/serial-squid/sch/squid-sch.pdf

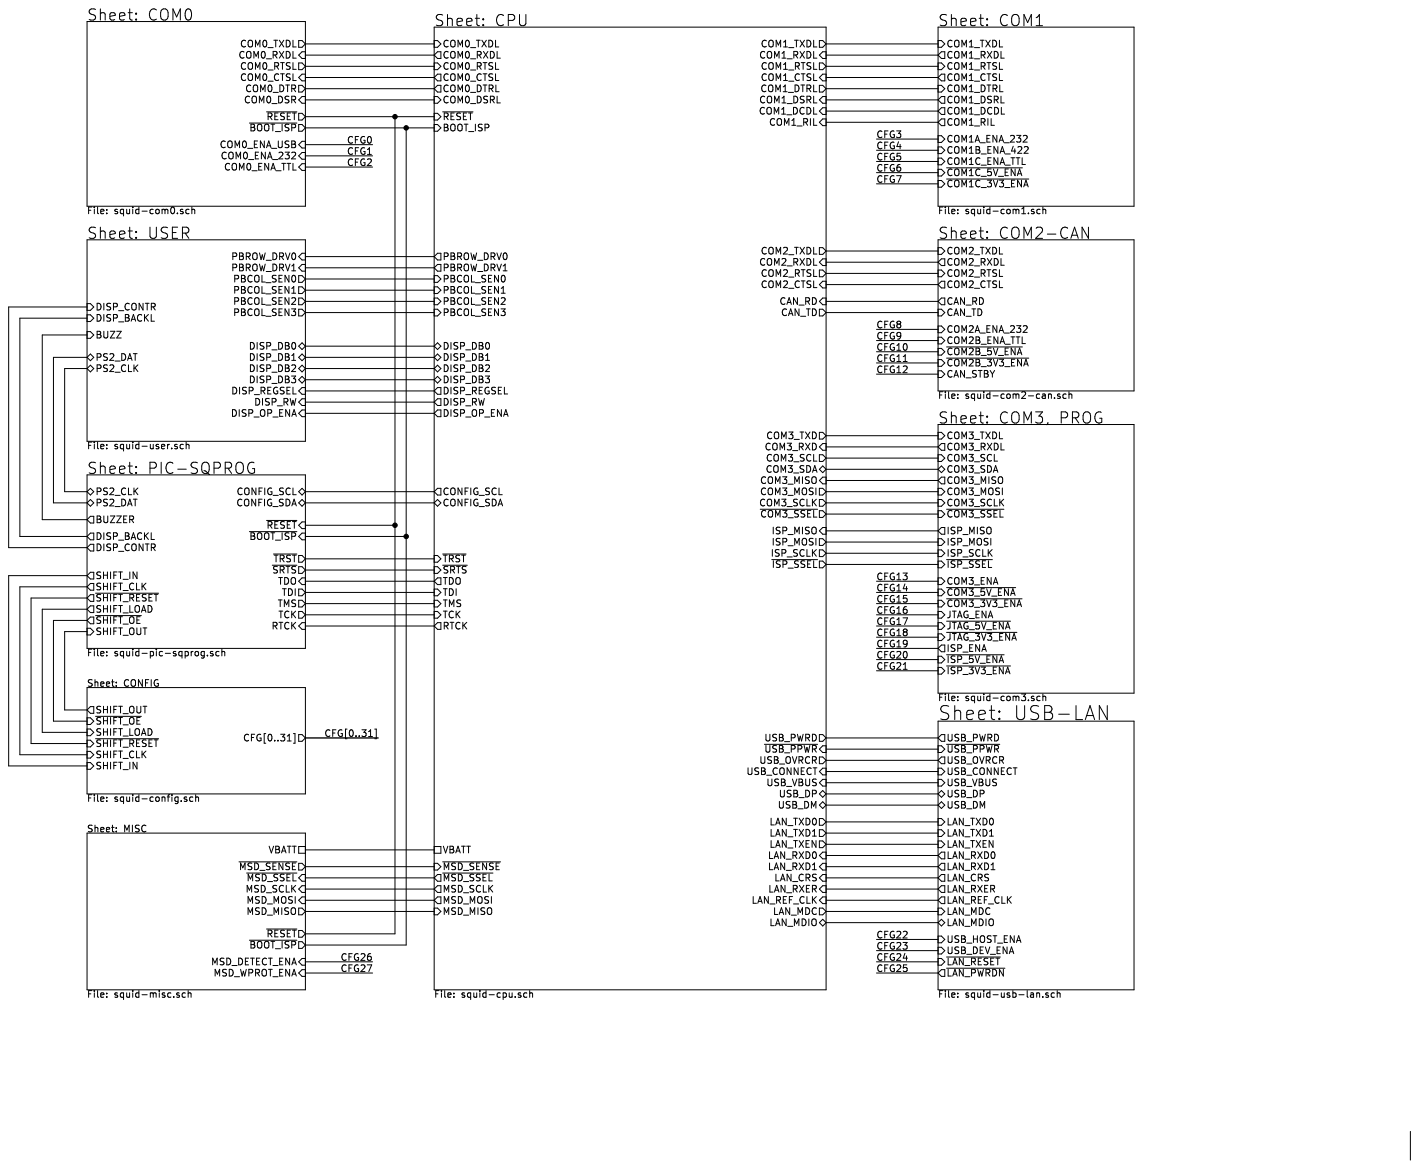
[picture p34: page 1]

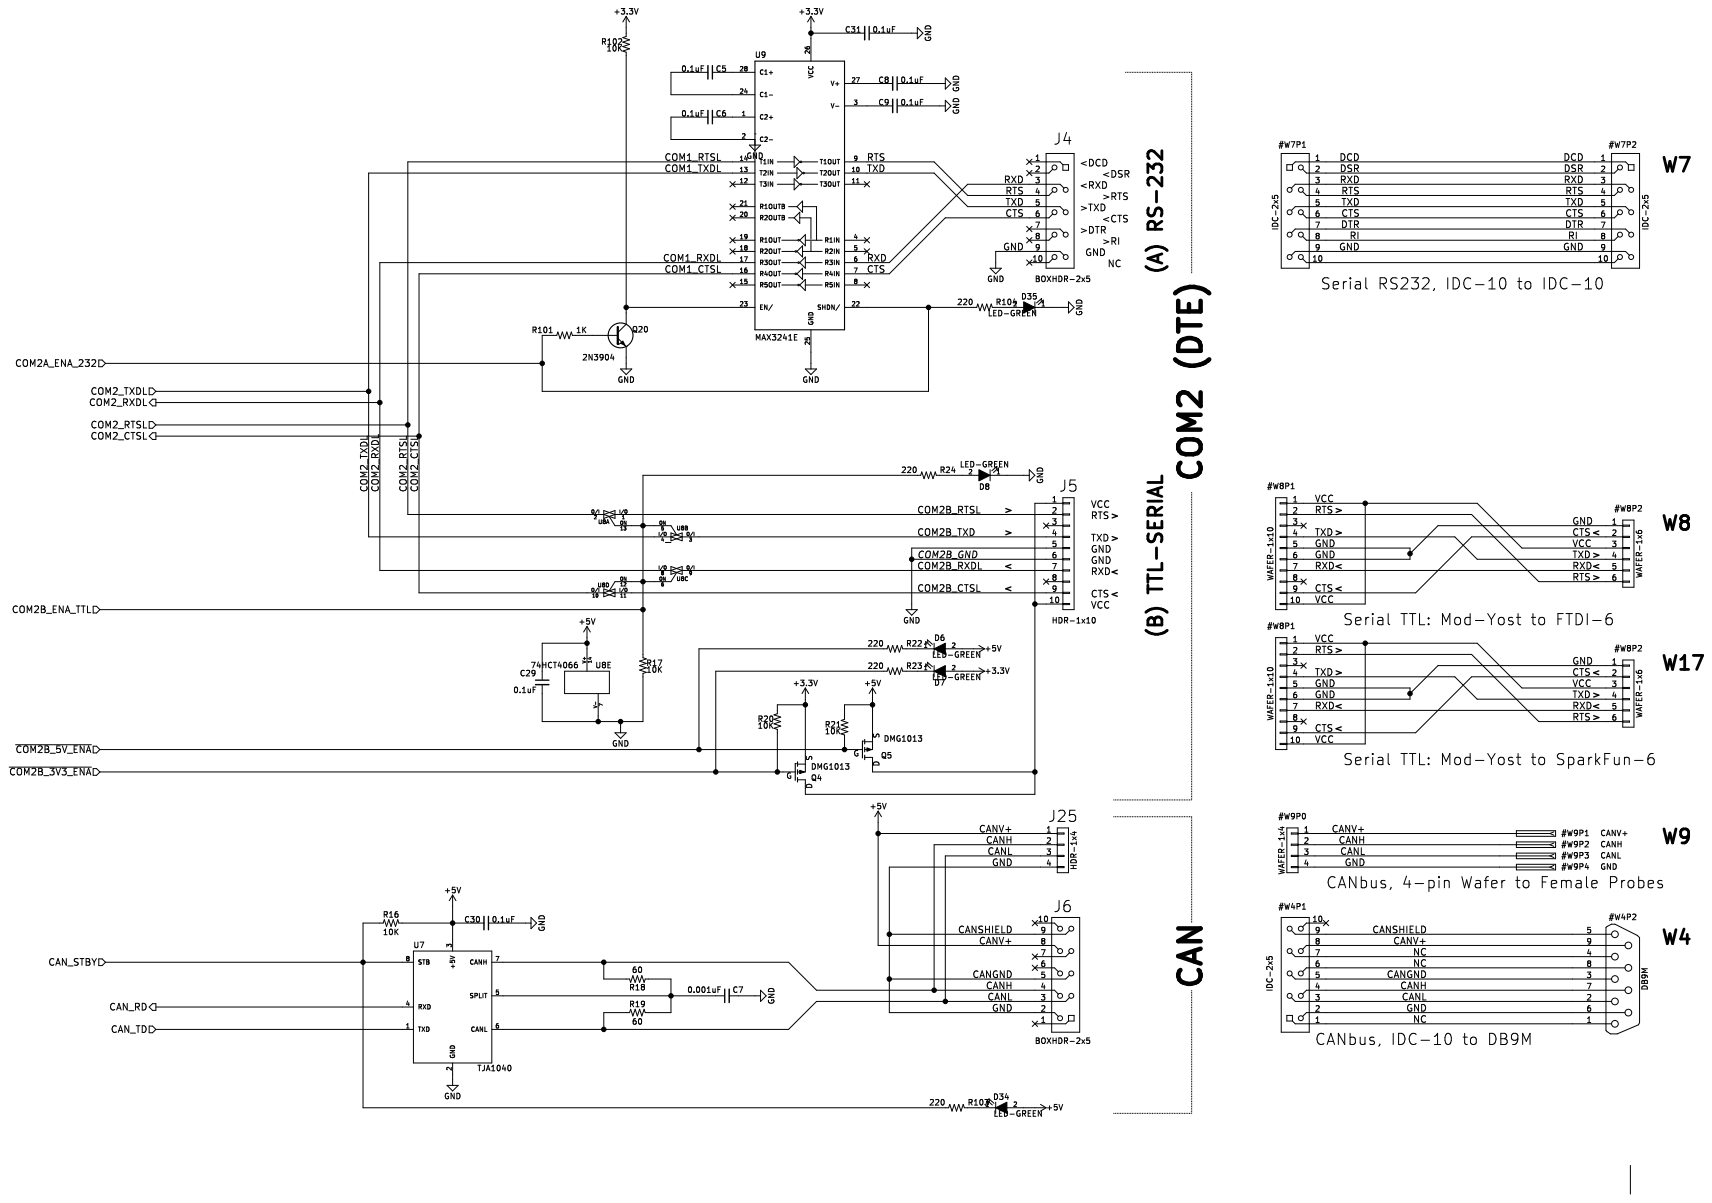
[picture p35: page 2]

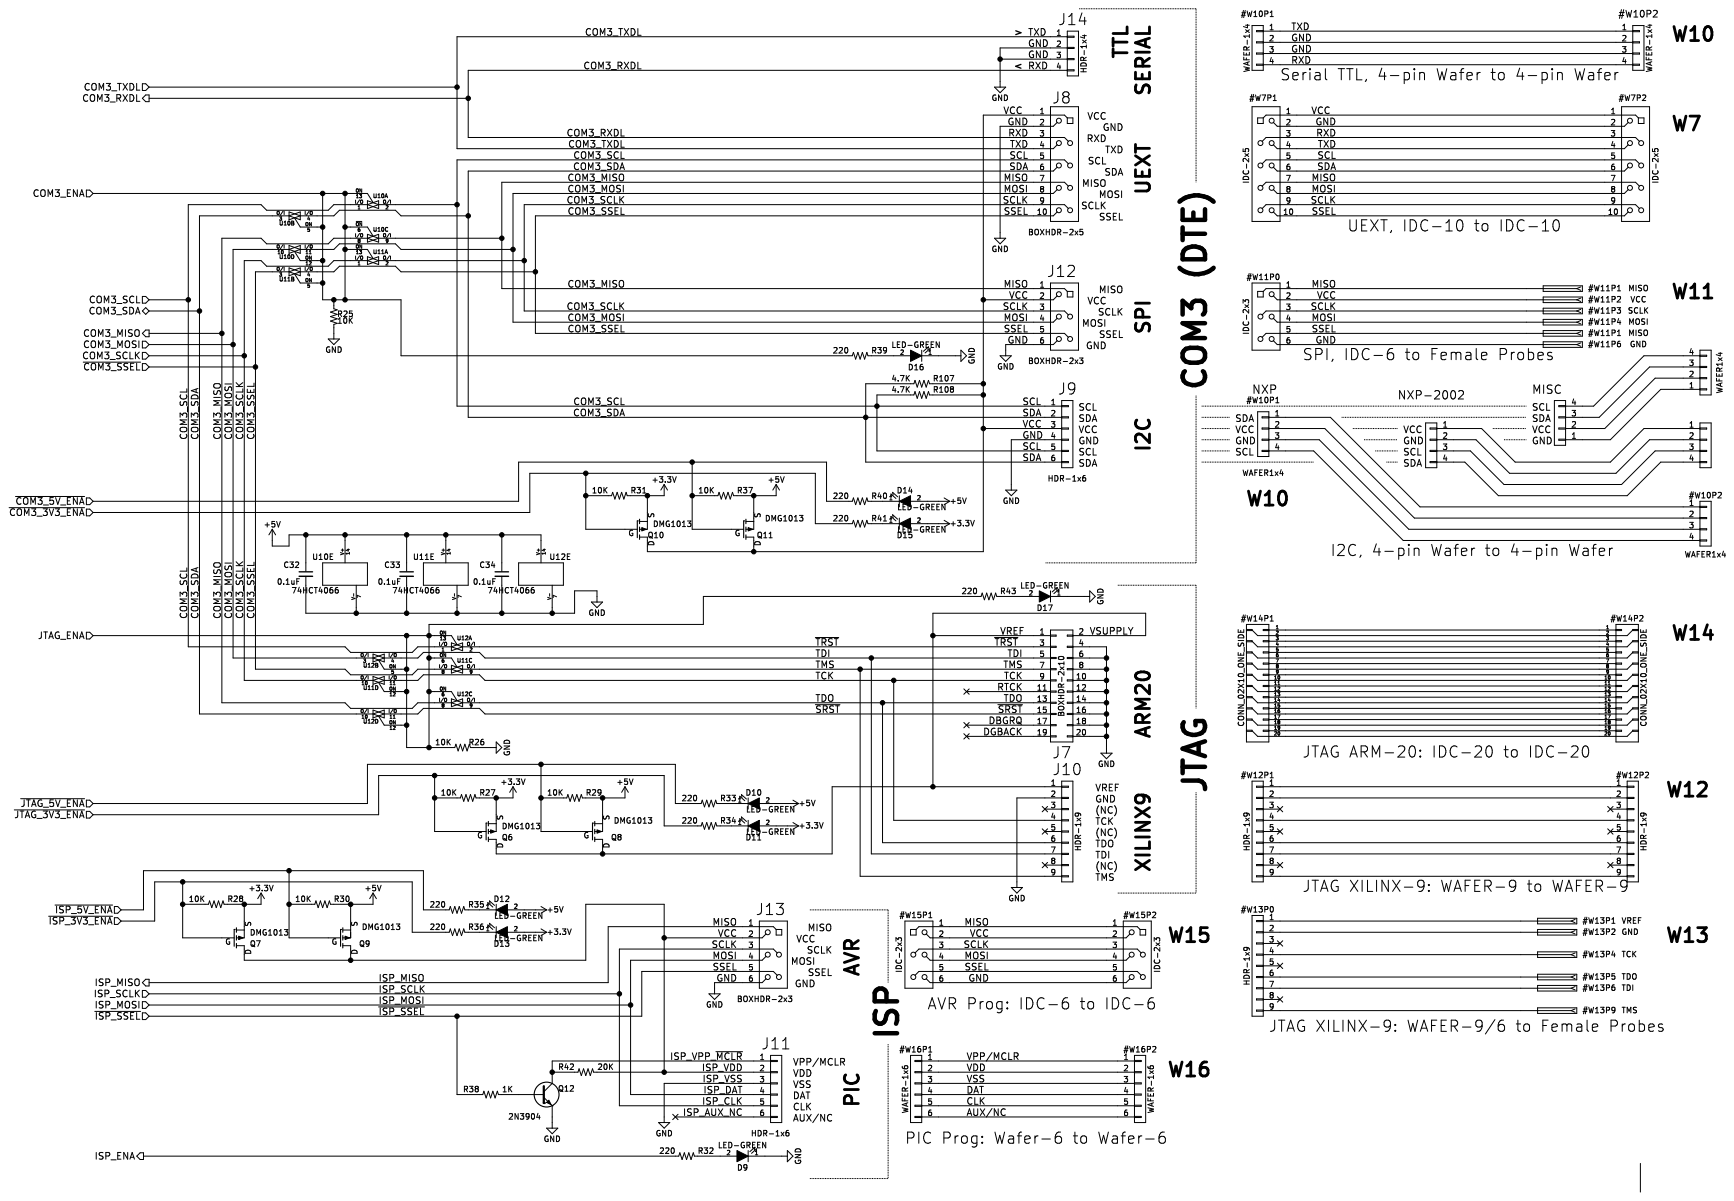
[picture p36: page 3]

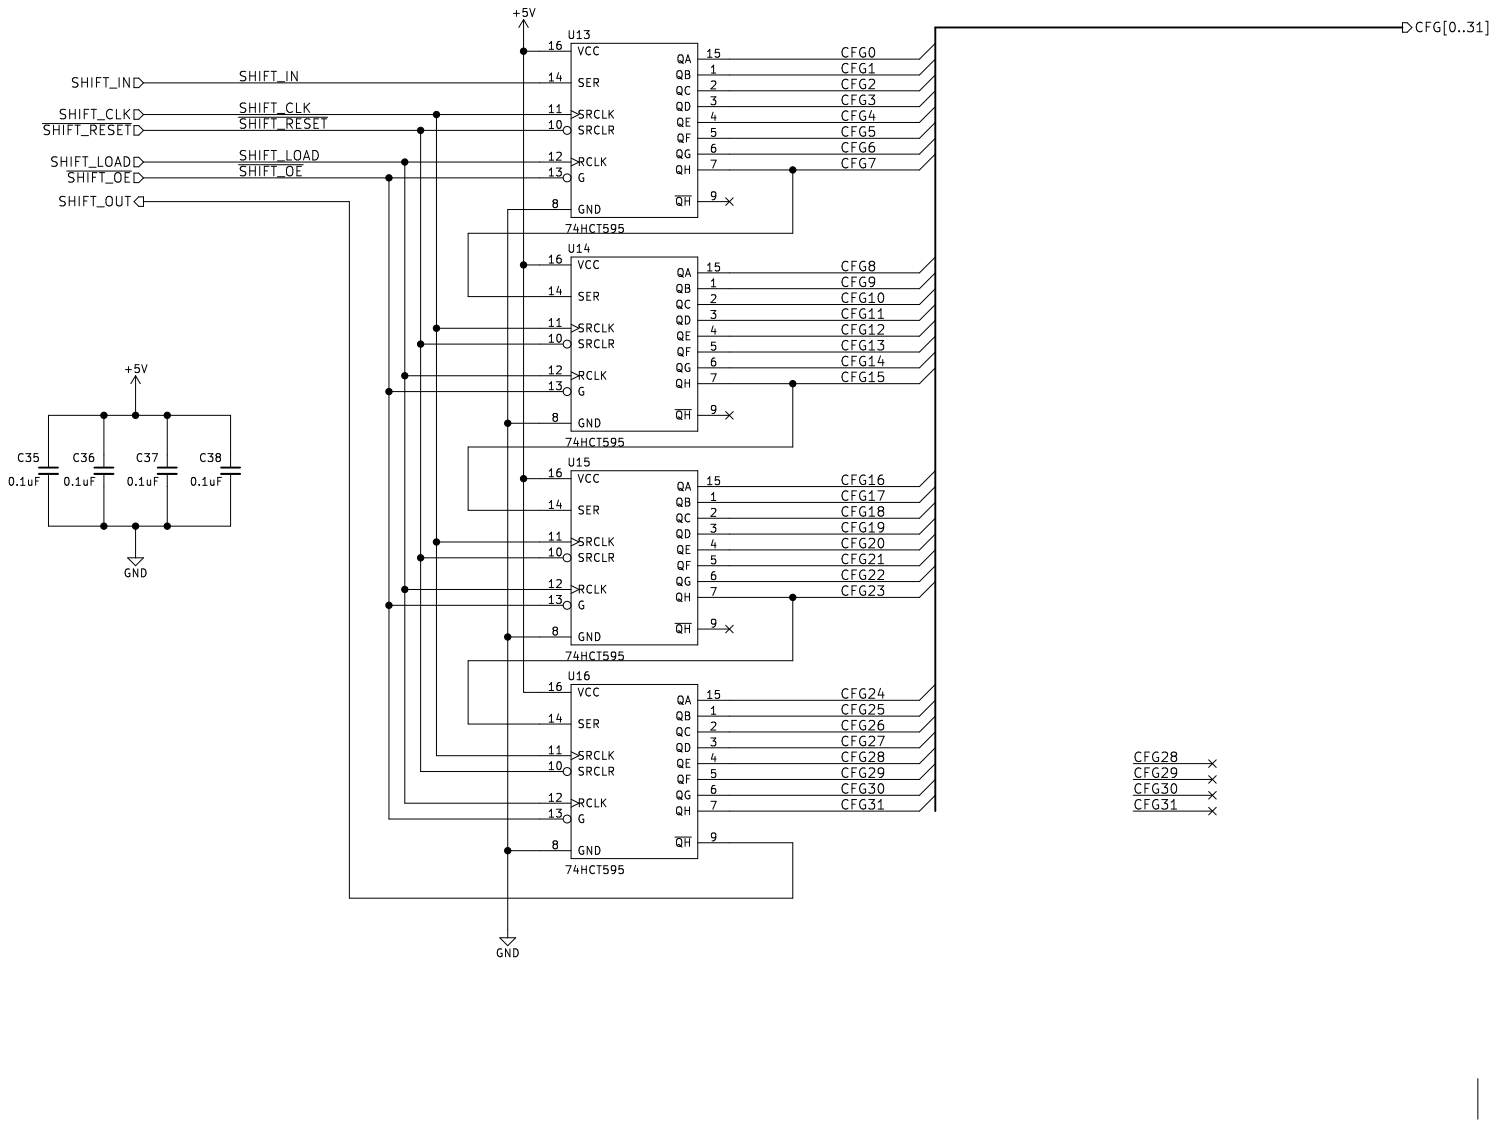
[picture p37: page 4]

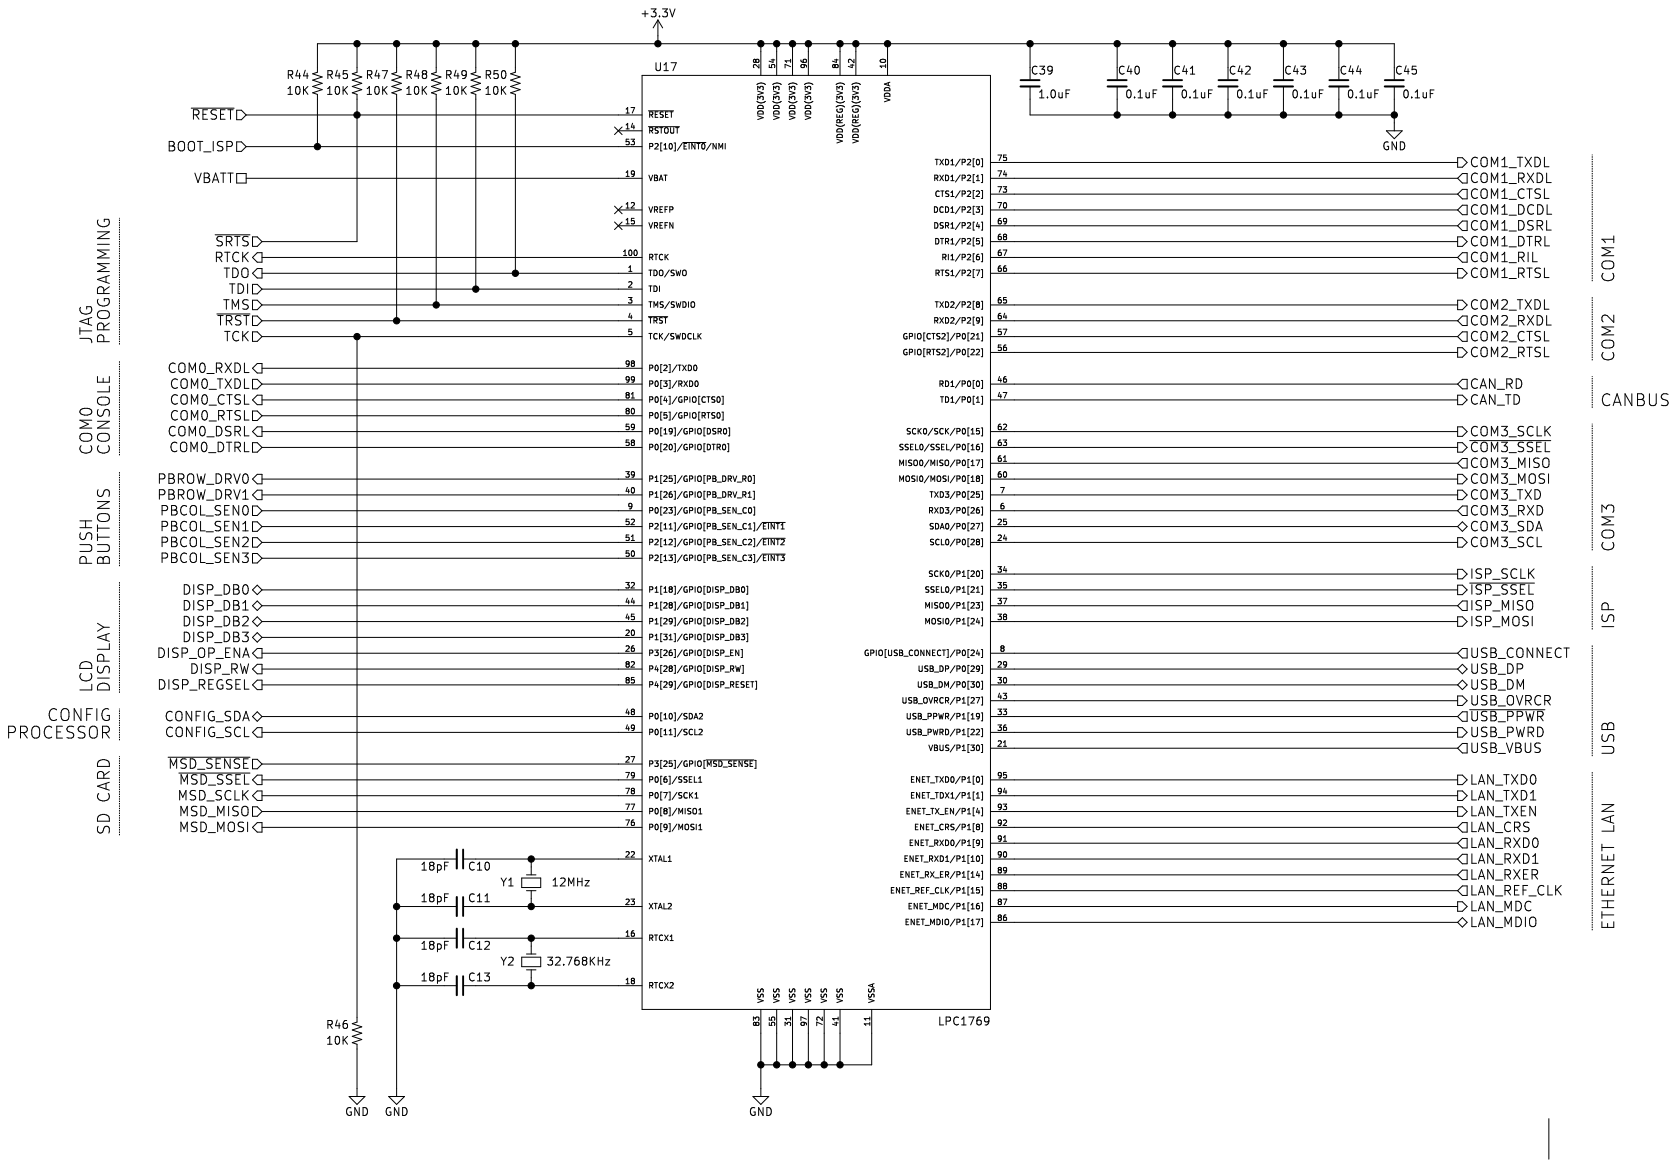
[picture p38: page 5]

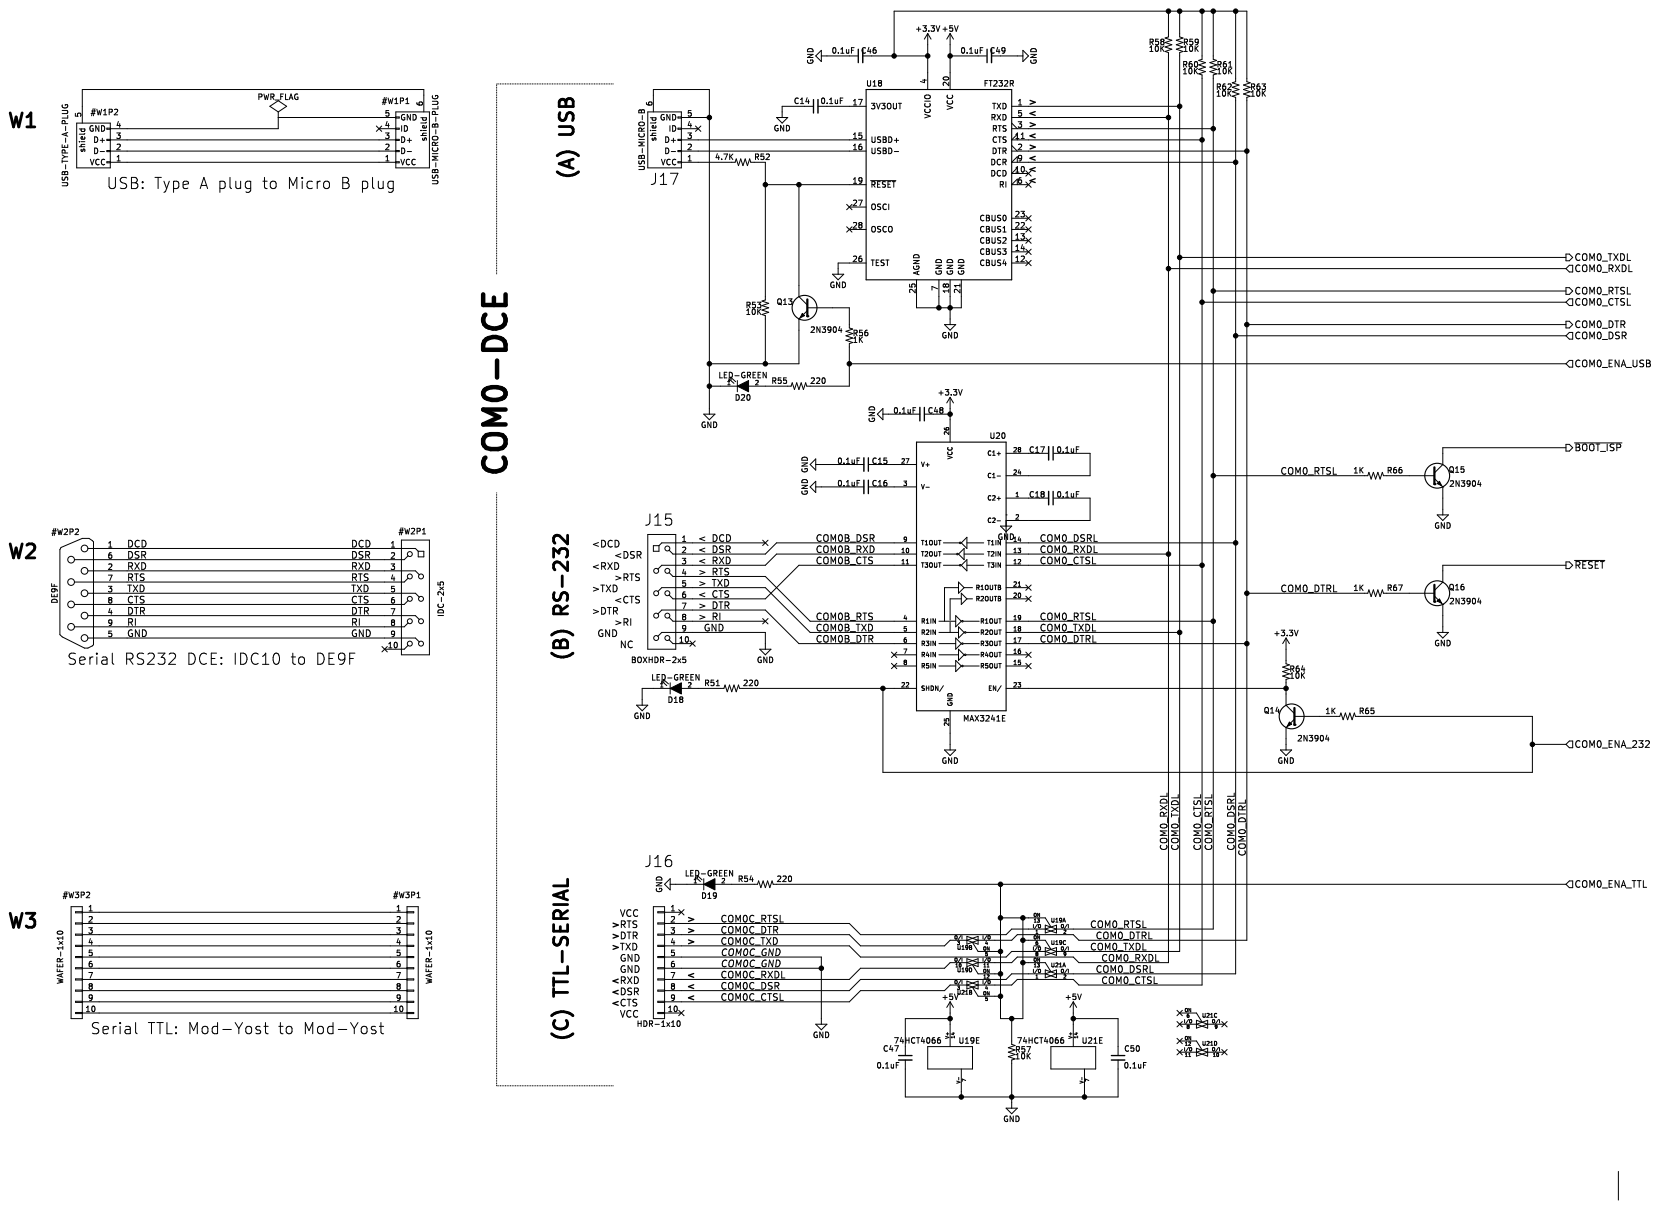
[picture p39: page 6]

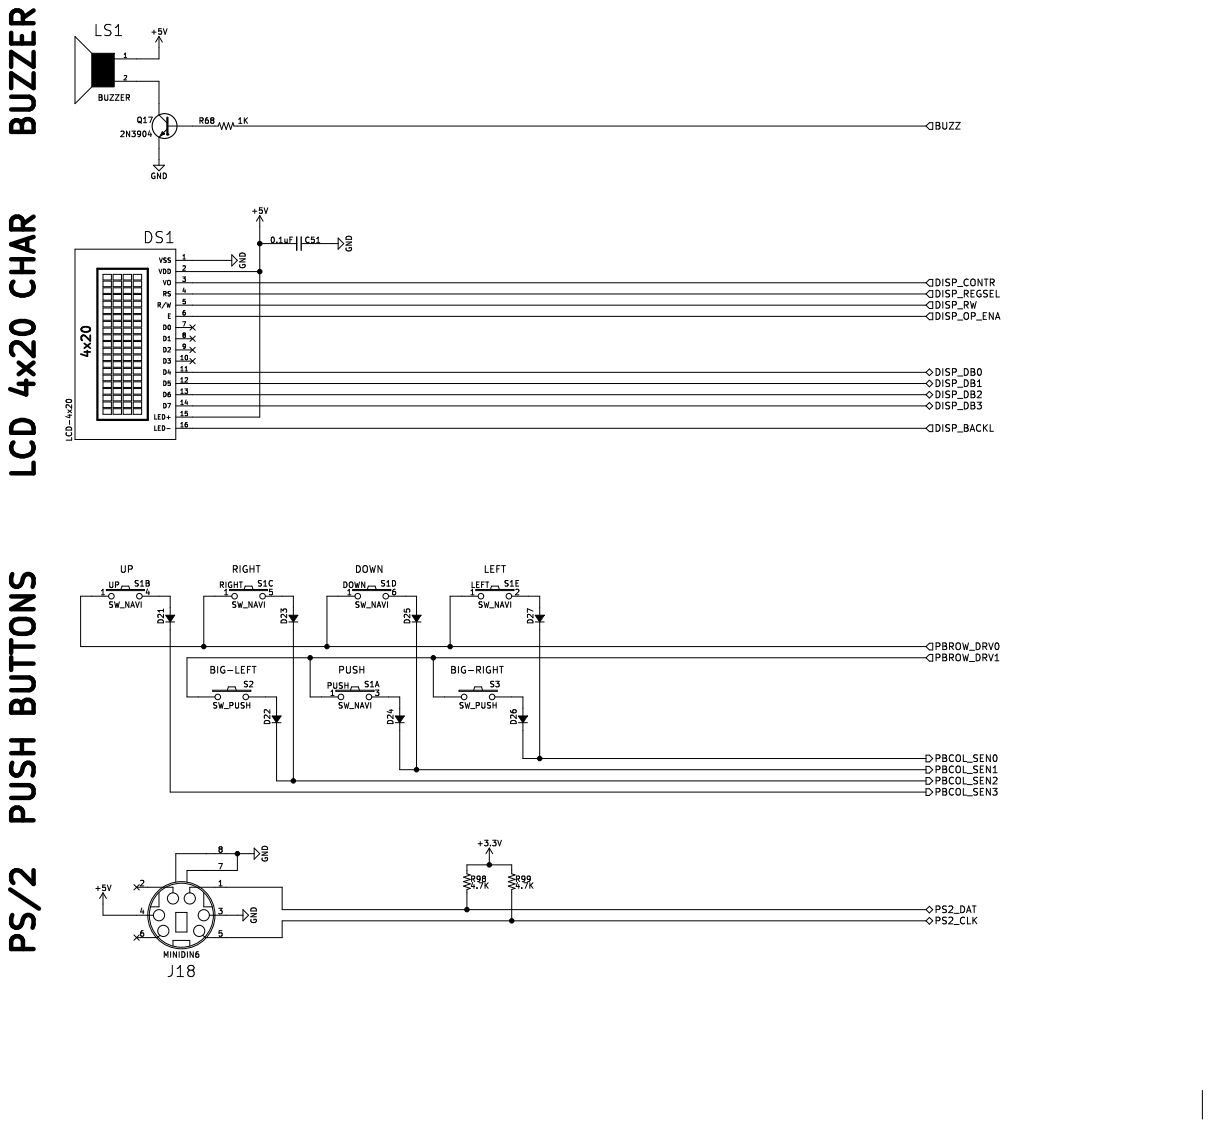
[picture p40: page 7]

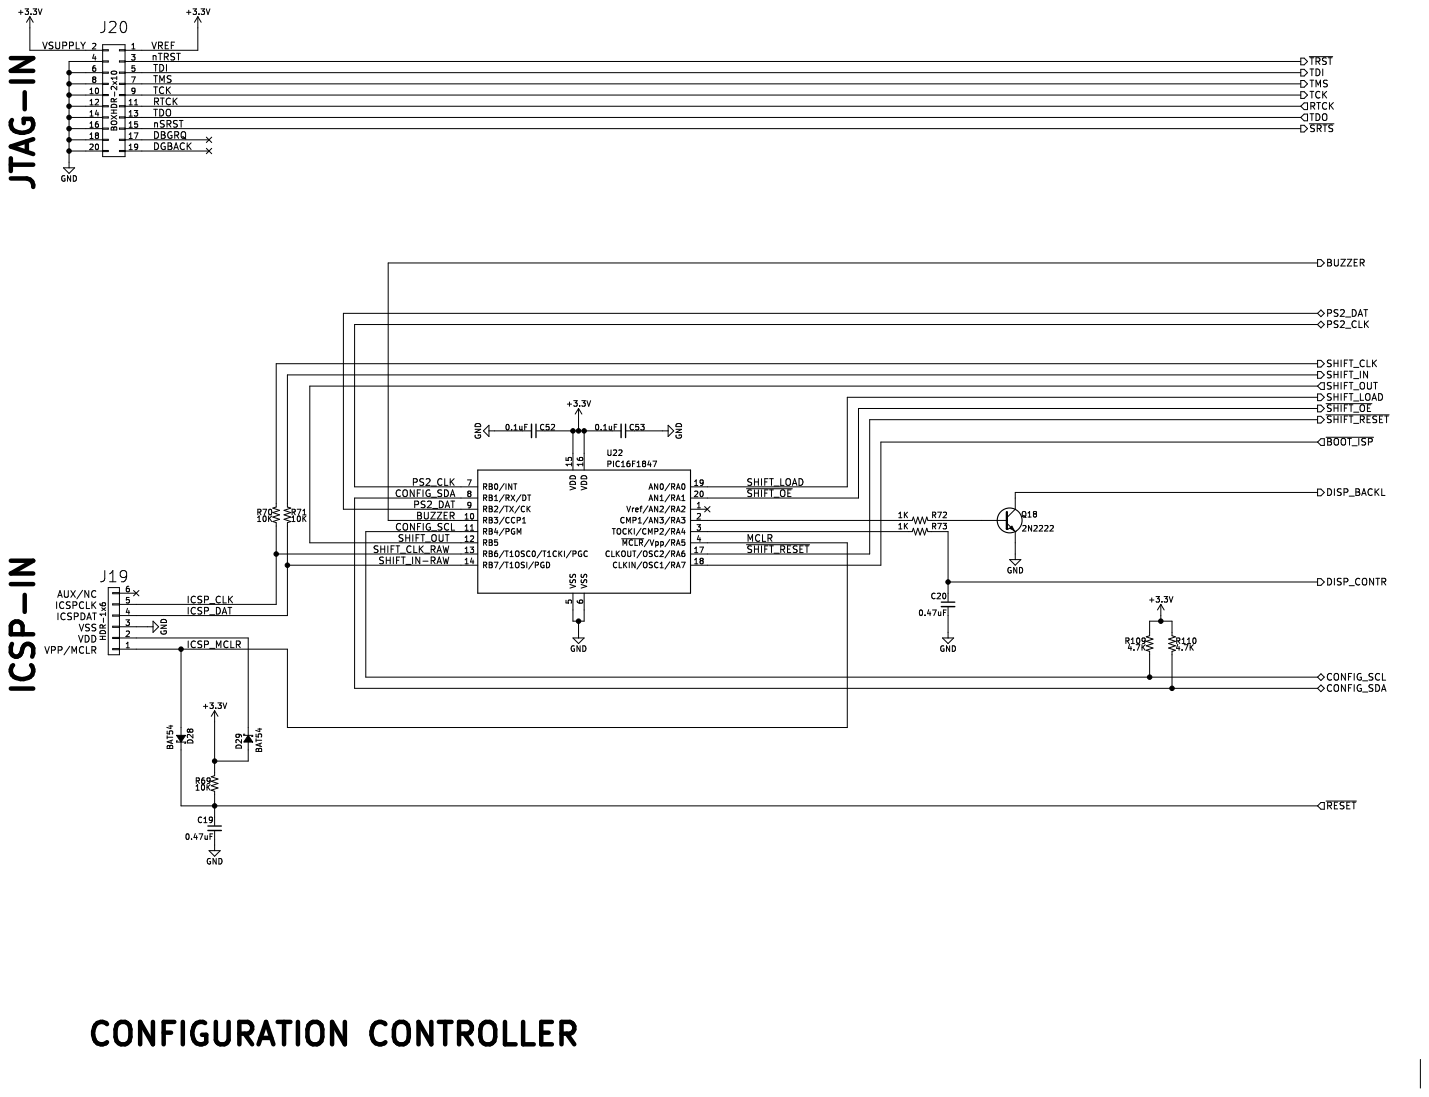
[picture p41: page 8]

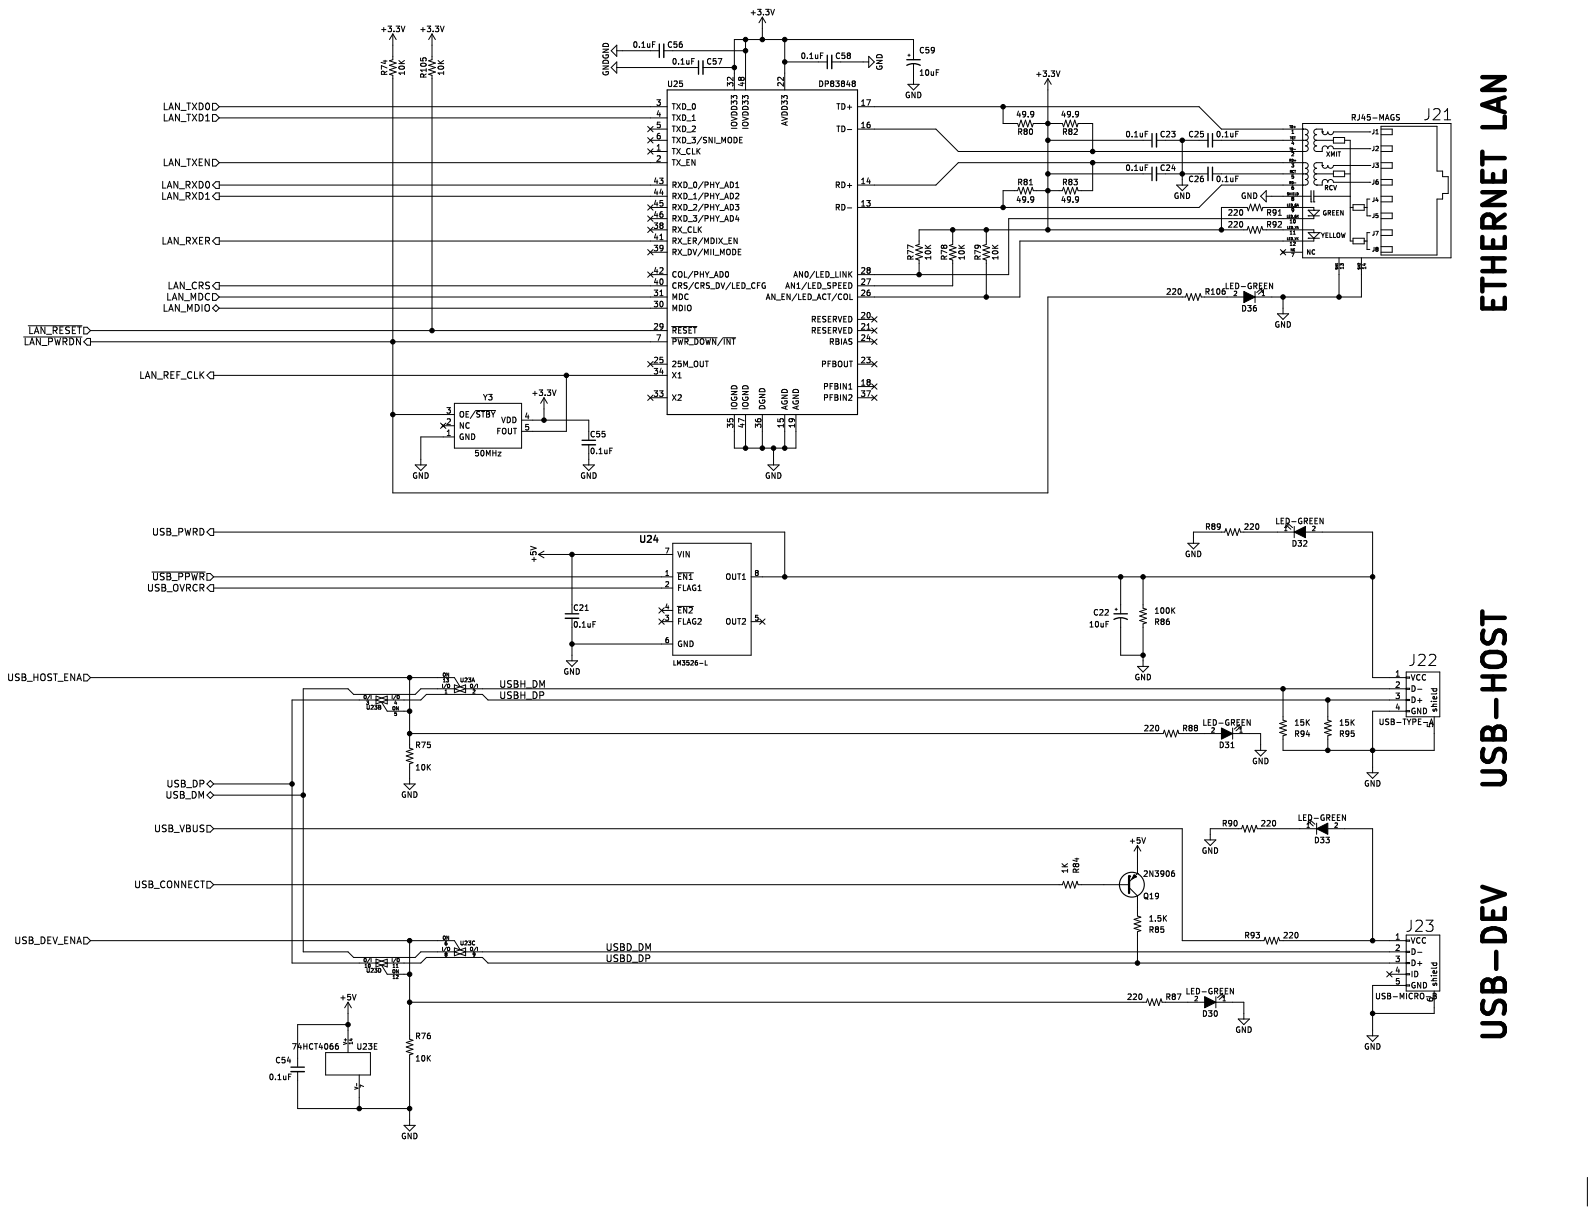
[picture p42: page 9]

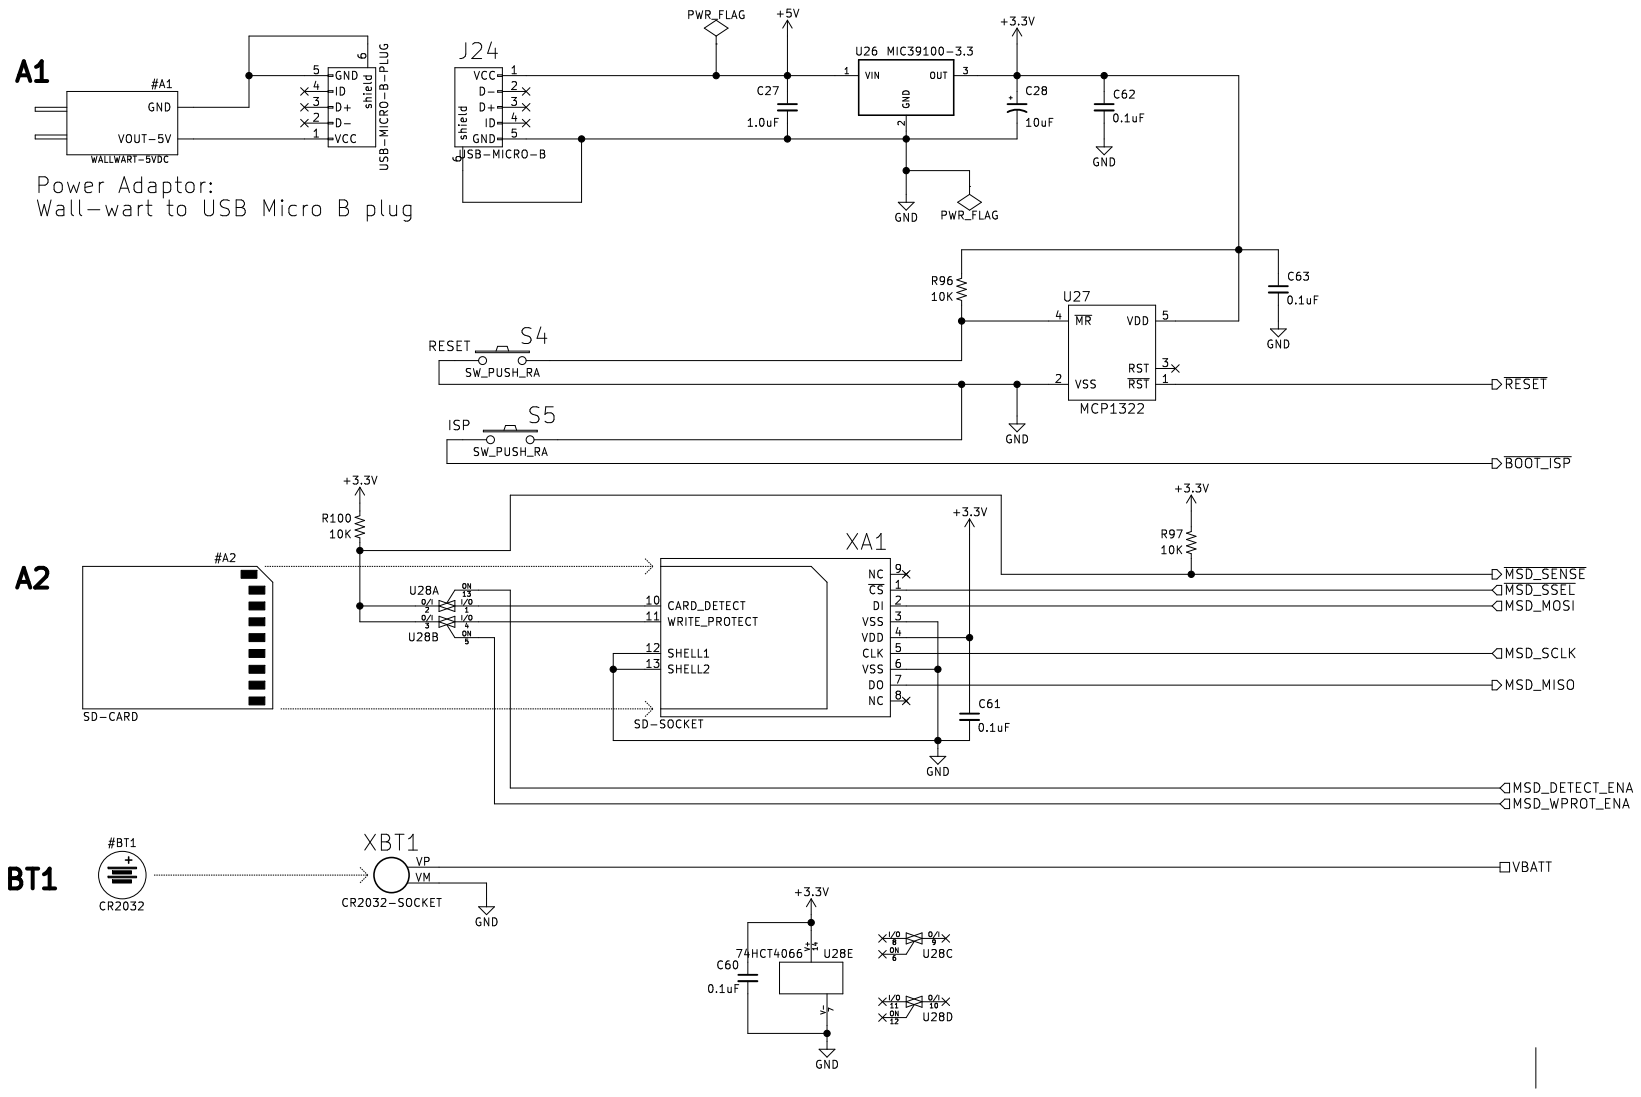
[picture p43: page 10]

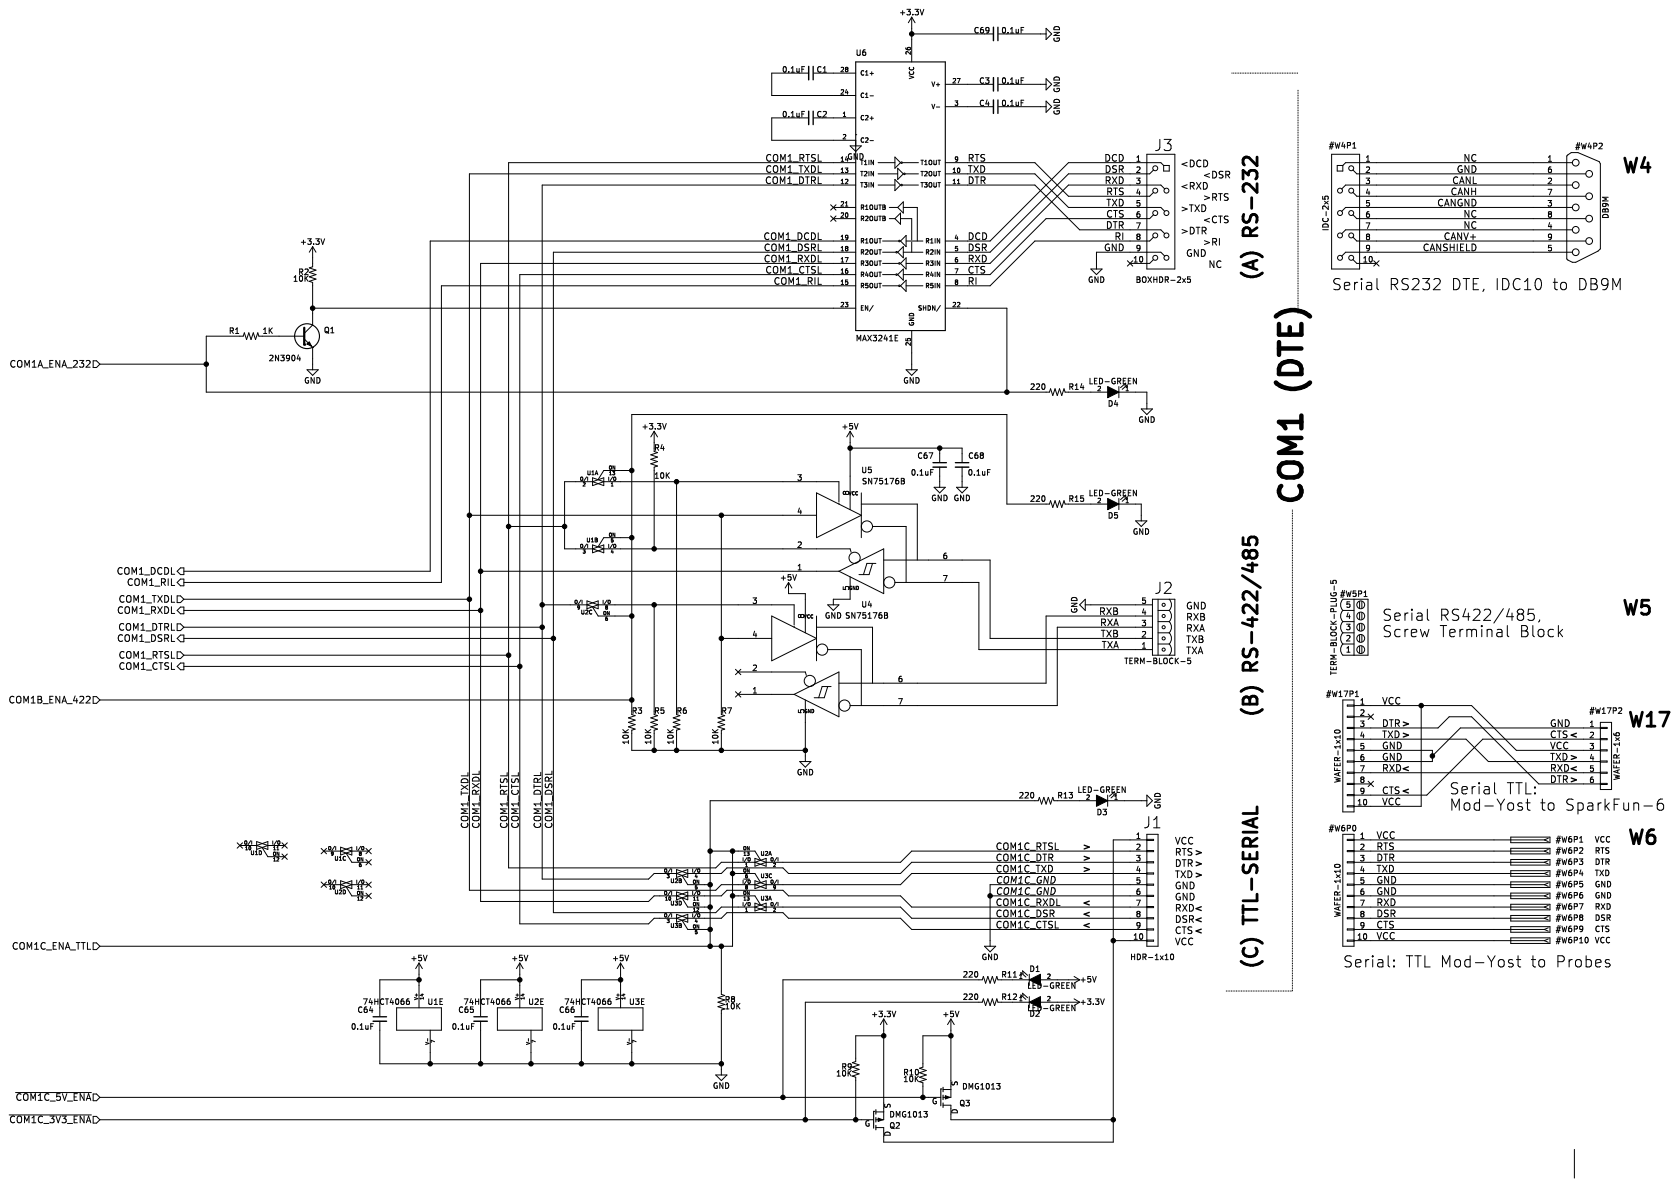
[picture p44: page 11]
