thestumbler/serial-squid/docs/connector-figure-with-table.pdf

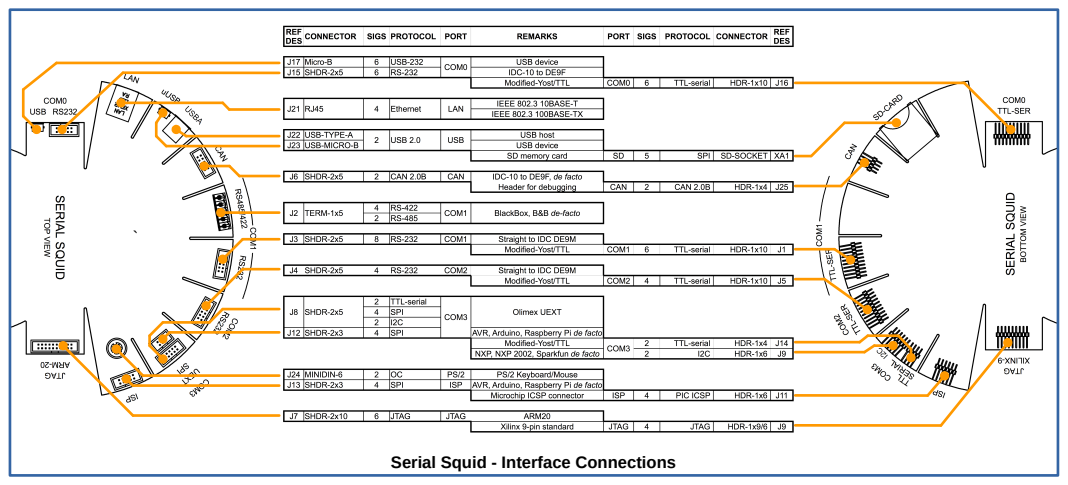
[picture p45: page 1]

Serial Squid - Interface Connections
