thestumbler/serial-squid/docs/squid-drawing-top-view.pdf

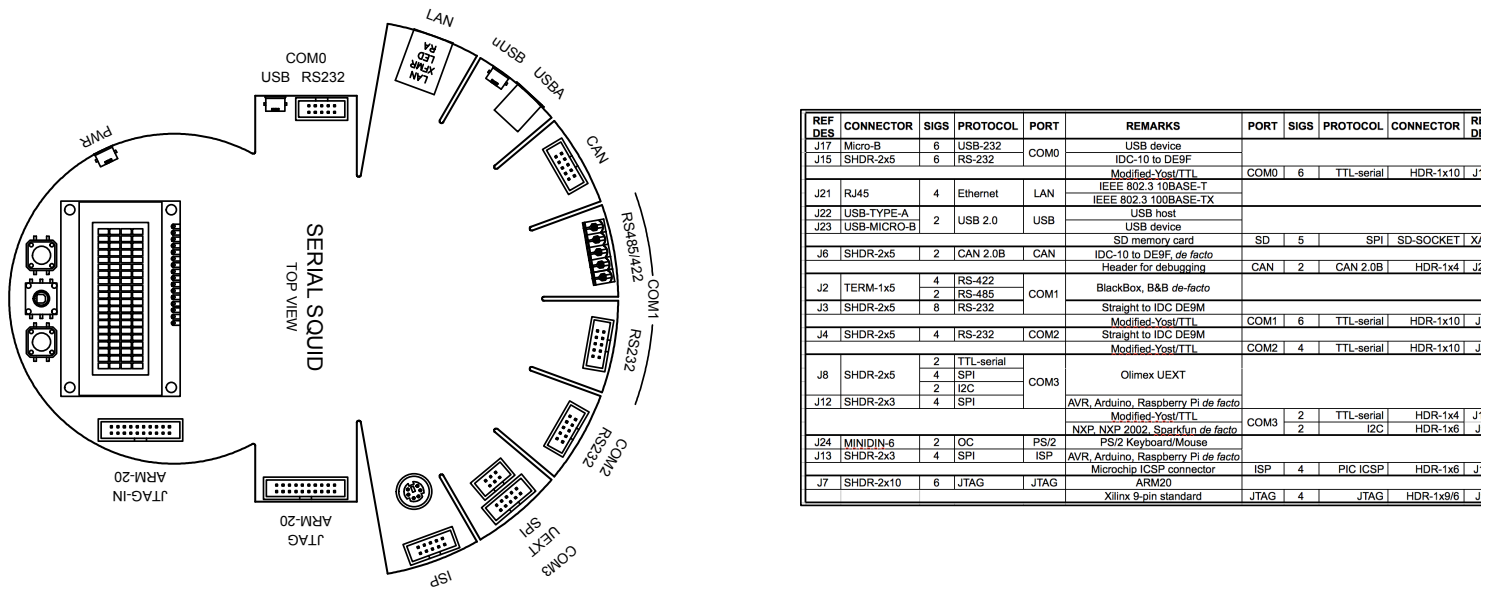
[picture p46: page 1]
LAN; CAN RS485/422 RS232 COM2 RS232; COM0; USB; SERIAL SQUID; TOP VIEW; COM1; USBA; uUSB
