thestumbler/serial-squid/mech/squid-mech-bot-view.pdf

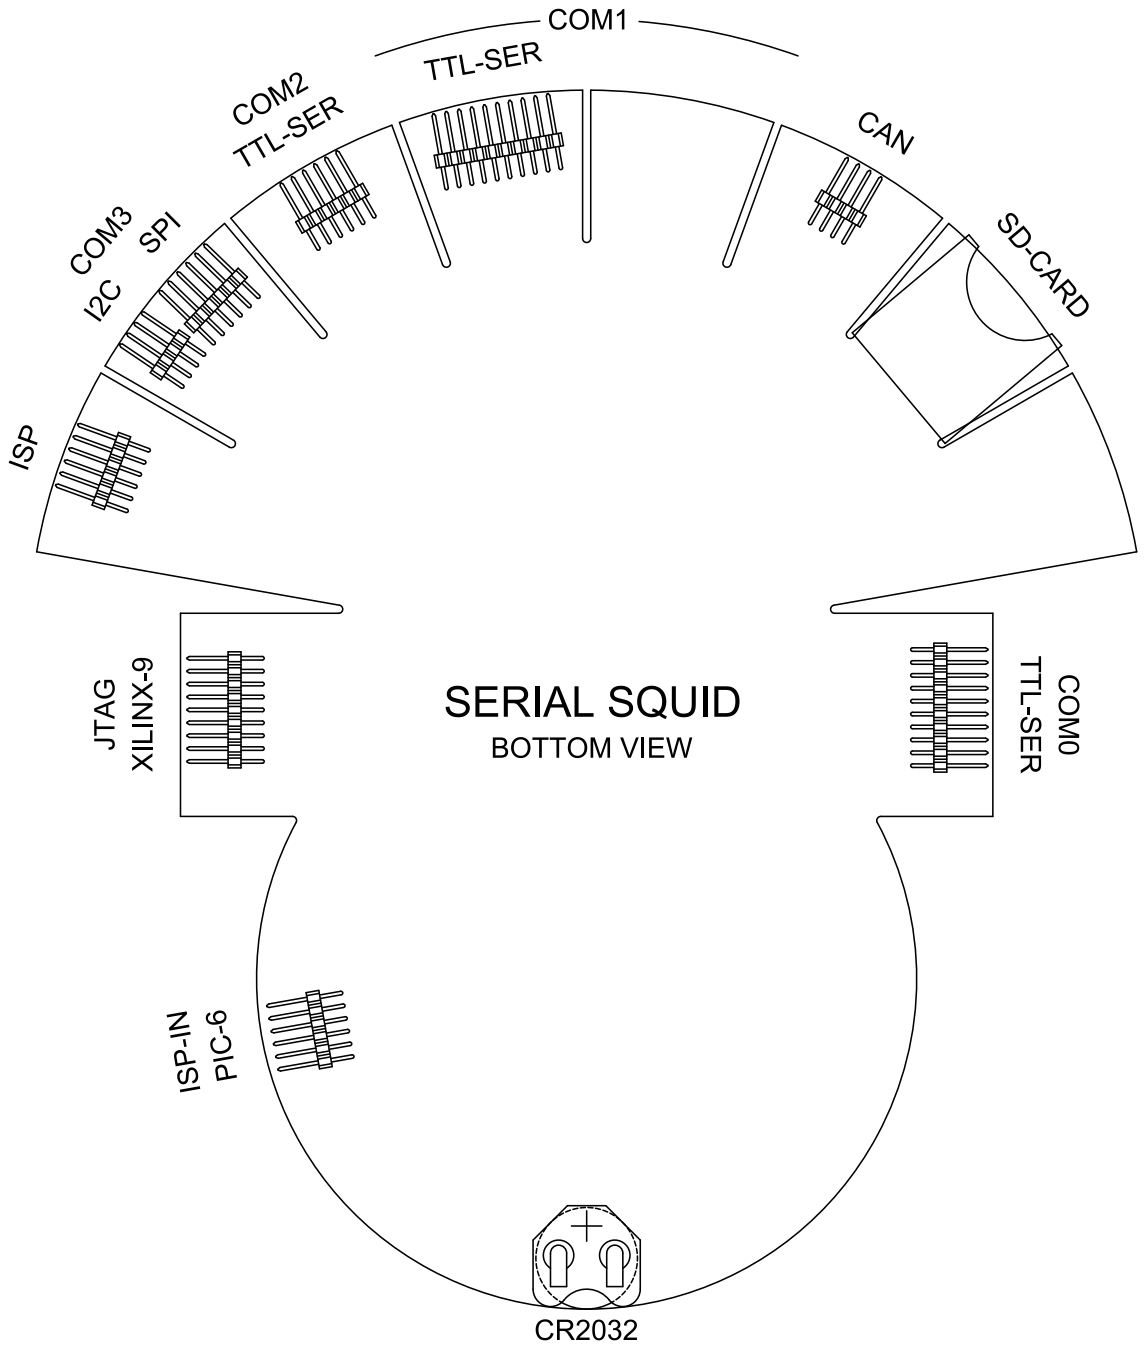
[picture p47: page 1]
