thestumbler/serial-squid/mech/squid-mech-top-view.pdf

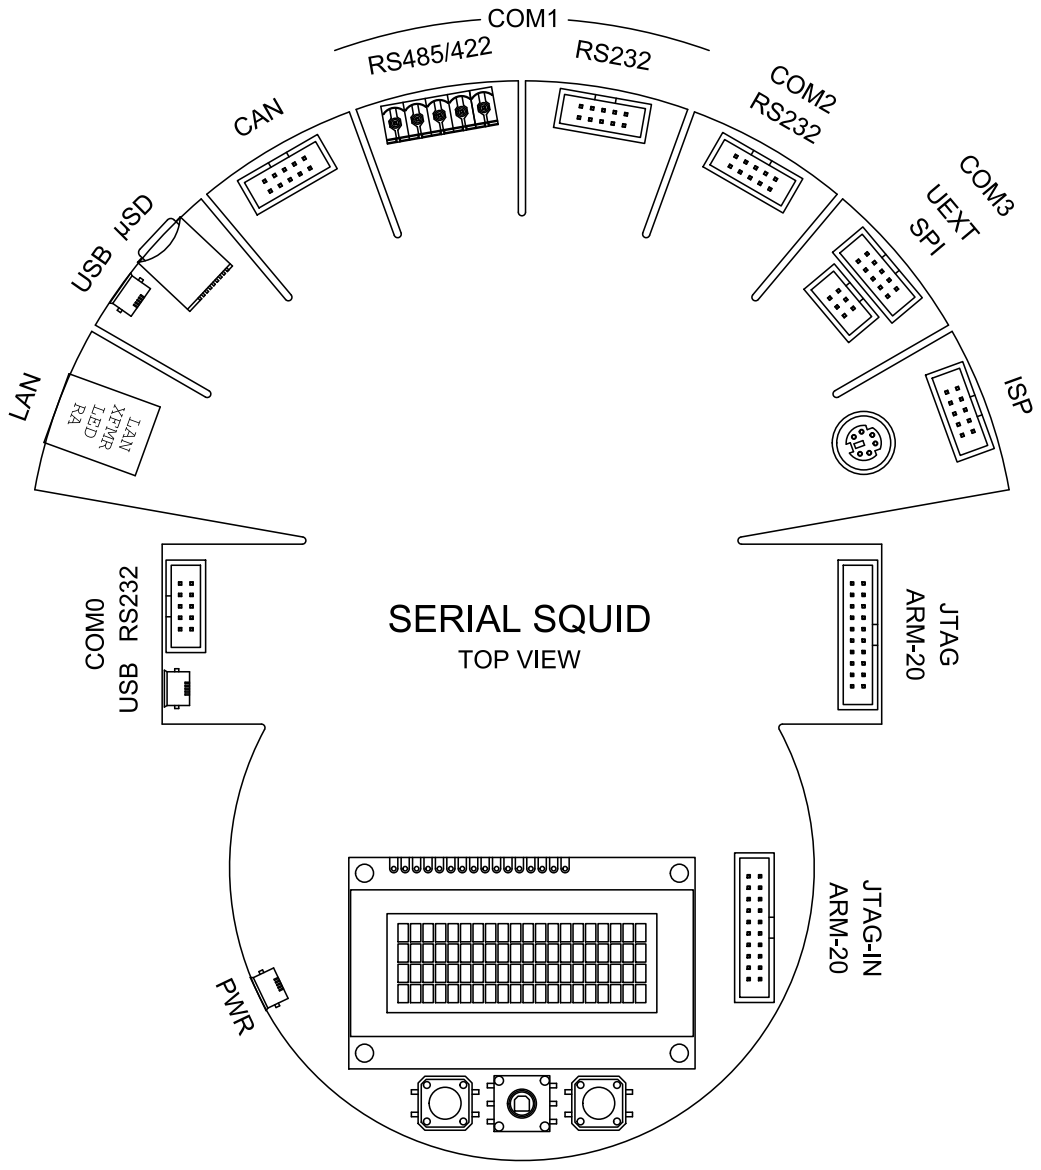
[picture p48: page 1]
